turkmanovic/OpenEPT/GUI/OpenEPT/images/timerOn.png

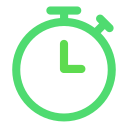
GUI/OpenEPT/images/timerOn.png
