turkmanovic/OpenEPT/Hardware/Source Files KiCad/ALTIUM_EMBEDDED_MODELS/DPAK254P1524X483-3L.step

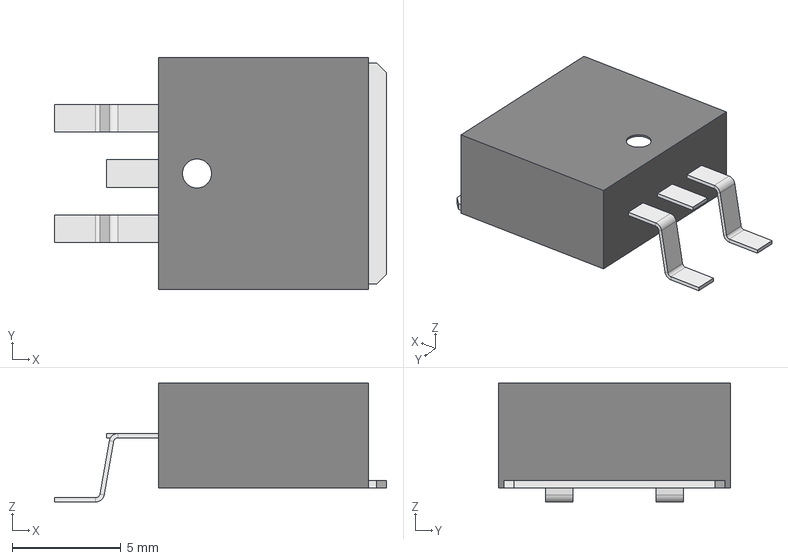
[picture p17: CAD file, 2024-06-27]
Hardware/Source Files KiCad/ALTIUM_EMBEDDED_MODELS/DPAK254P1524X483-3L.step
15.2 x 10.7 x 5.46 mm
Lead x 2
Trimmed Lead
