turkmanovic/OpenEPT/Hardware/Source Files KiCad/ALTIUM_EMBEDDED_MODELS/c-282834-2-c-3d.stp

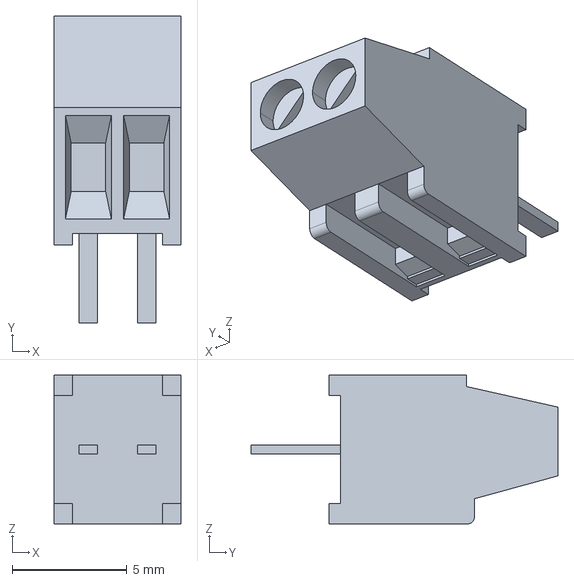
[picture p18: CAD file, 2024-06-27]
Hardware/Source Files KiCad/ALTIUM_EMBEDDED_MODELS/c-282834-2-c-3d.stp
5.54 x 13.4 x 6.50 mm
