turkmanovic/OpenEPT/Hardware/Source Files KiCad/ALTIUM_EMBEDDED_MODELS/User Library-CR3216-1206.step

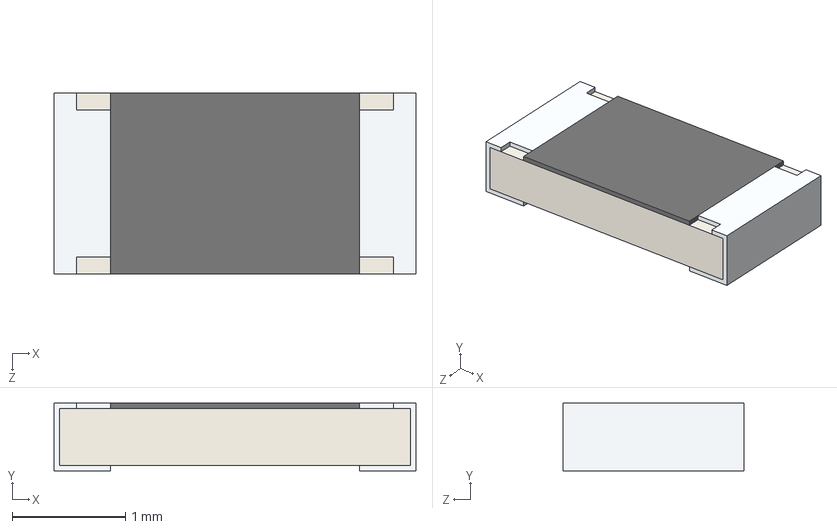
[picture p19: CAD file, 2024-06-27]
Hardware/Source Files KiCad/ALTIUM_EMBEDDED_MODELS/User Library-CR3216-1206.step
3.20 x 0.6 x 1.60 mm
