turkmanovic/OpenEPT/Hardware/Source Files KiCad/ALTIUM_EMBEDDED_MODELS/User Library-User Library-CAP_Al_SMD_6_3x7_7mm.step

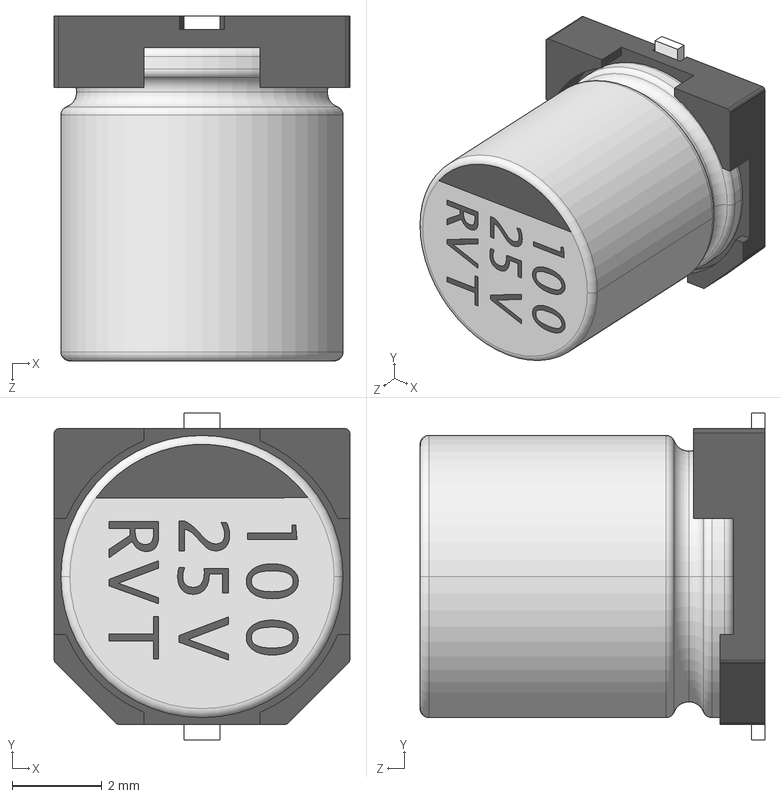
[picture p20: CAD file, 2024-06-27]
Hardware/Source Files KiCad/ALTIUM_EMBEDDED_MODELS/User Library-User Library-CAP_Al_SMD_6_3x7_7mm.step
6.60 x 7.30 x 7.70 mm
