turkmanovic/OpenEPT/Hardware/Source Files KiCad/ALTIUM_EMBEDDED_MODELS/DIOM5026X23N.step

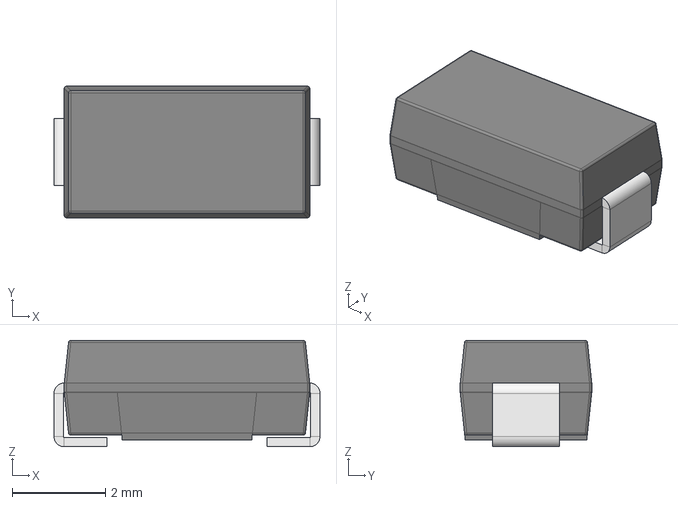
[picture p21: CAD file, 2024-06-27]
Hardware/Source Files KiCad/ALTIUM_EMBEDDED_MODELS/DIOM5026X23N.step
5.72 x 2.83 x 2.29 mm
Lead x 2
