turkmanovic/OpenEPT/Hardware/Source Files KiCad/ALTIUM_EMBEDDED_MODELS/SOIC127P600X175-8N.step

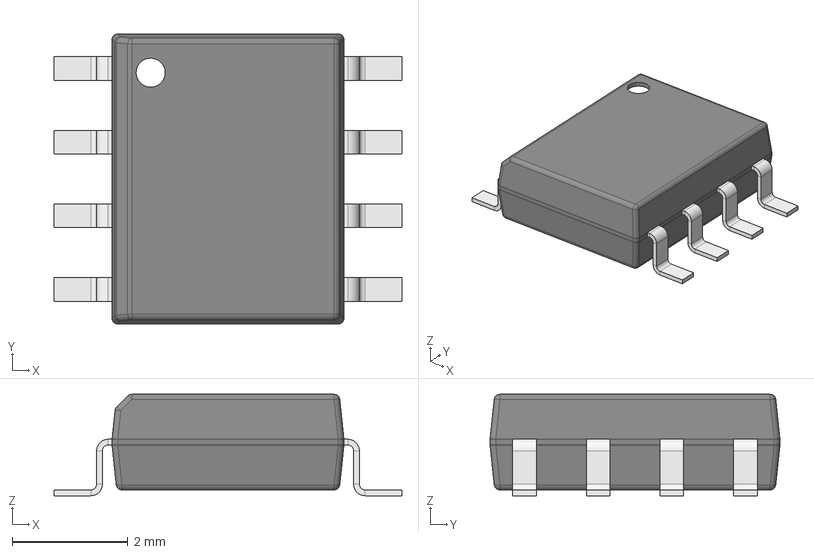
[picture p22: CAD file, 2024-06-27]
Hardware/Source Files KiCad/ALTIUM_EMBEDDED_MODELS/SOIC127P600X175-8N.step
6.00 x 5.00 x 1.75 mm
Leader x 8
