turkmanovic/OpenEPT/Hardware/Source Files KiCad/ALTIUM_EMBEDDED_MODELS/User Library-SMD Polymer Aluminum Electrolytic Capacitors B6 22uF 16V.step

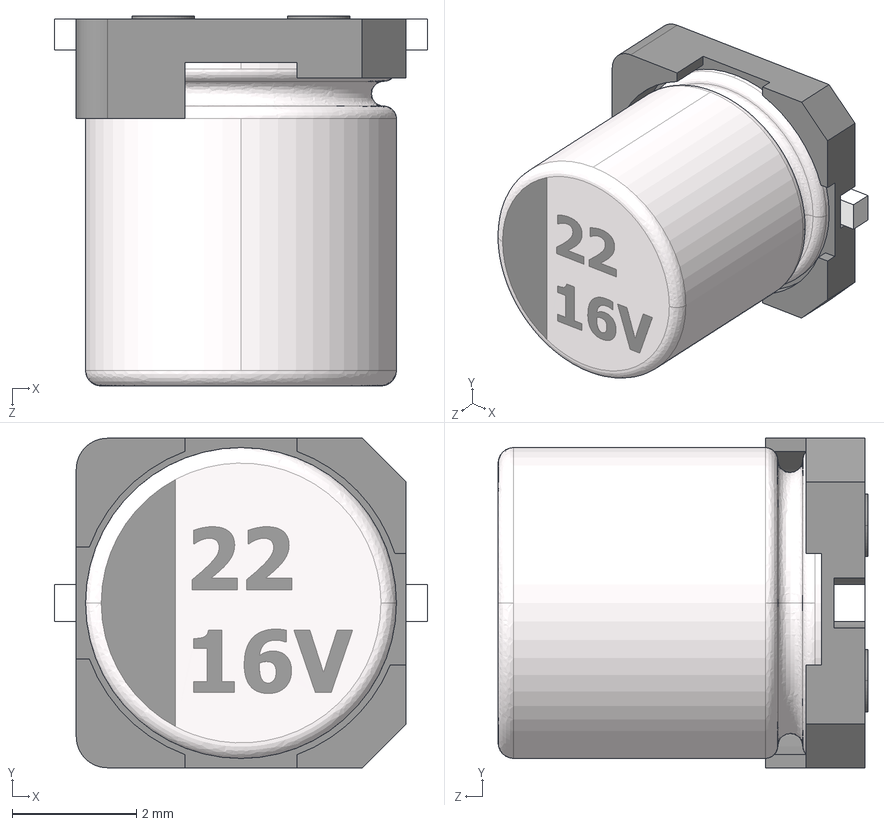
[picture p23: CAD file, 2024-06-27]
Hardware/Source Files KiCad/ALTIUM_EMBEDDED_MODELS/User Library-SMD Polymer Aluminum Electrolytic Capacitors B6 22uF 16V.step
6.00 x 5.30 x 5.95 mm
