turkmanovic/OpenEPT/Hardware/Source Files KiCad/ALTIUM_EMBEDDED_MODELS/User Library-sw_diptronics_dtsm-61r-b.step

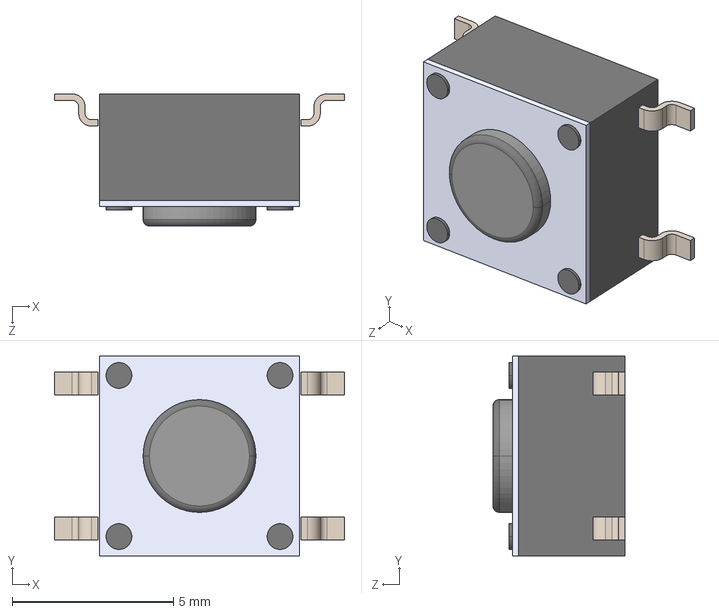
[picture p24: CAD file, 2024-06-27]
Hardware/Source Files KiCad/ALTIUM_EMBEDDED_MODELS/User Library-sw_diptronics_dtsm-61r-b.step
9.00 x 6.20 x 4.10 mm
