turkmanovic/OpenEPT/Hardware/Source Files KiCad/ALTIUM_EMBEDDED_MODELS/User Library-UWT1C100MCL1GB.step

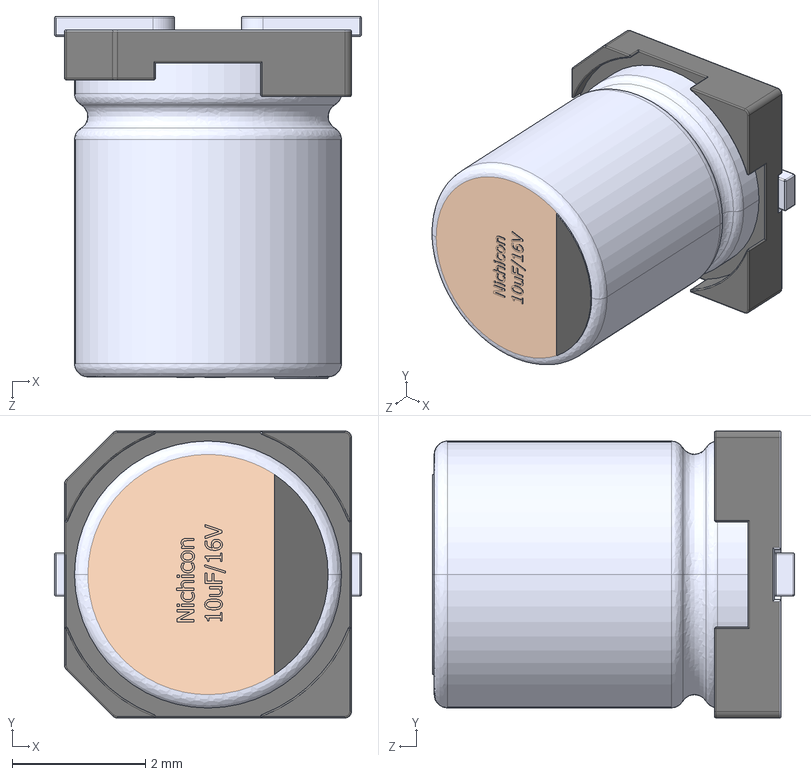
[picture p25: CAD file, 2024-06-27]
Hardware/Source Files KiCad/ALTIUM_EMBEDDED_MODELS/User Library-UWT1C100MCL1GB.step
4.60 x 4.30 x 5.43 mm
