turkmanovic/OpenEPT/Hardware/Source Files KiCad/ALTIUM_EMBEDDED_MODELS/SSQ-110-02-T-D-RA.stp

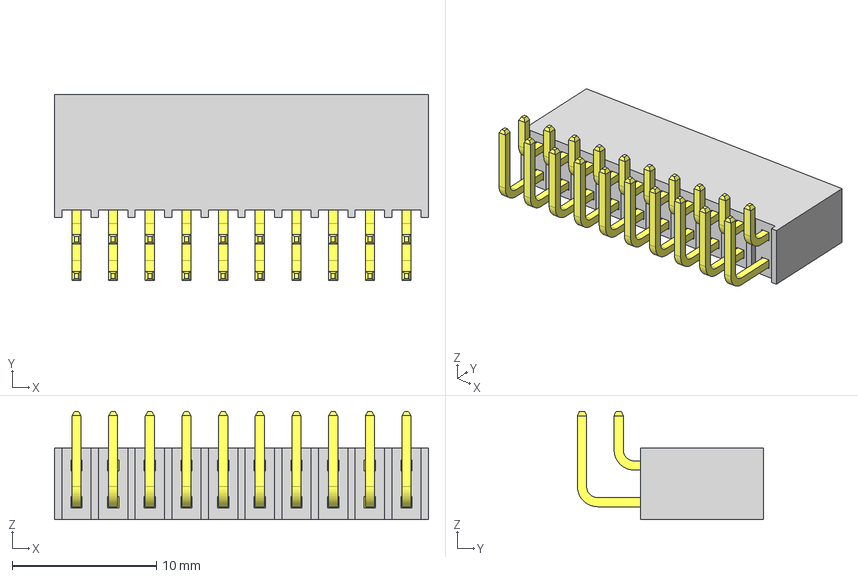
[picture p26: CAD file, 2024-06-27]
Hardware/Source Files KiCad/ALTIUM_EMBEDDED_MODELS/SSQ-110-02-T-D-RA.stp
25.9 x 12.9 x 7.49 mm
P2SSQ-110-02-T-D-RA
T1SSQ-110-02-T-D-RA
