turkmanovic/OpenEPT/GUI/OpenEPT/Chart/qcustomplot.h

/***************************************************************************
**                                                                        **
**  QCustomPlot, an easy to use, modern plotting widget for Qt            **
**  Copyright (C) 2011-2021 Emanuel Eichhammer                            **
**                                                                        **
**  This program is free software: you can redistribute it and/or modify  **
**  it under the terms of the GNU General Public License as published by  **
**  the Free Software Foundation, either version 3 of the License, or     **
**  (at your option) any later version.                                   **
**                                                                        **
**  This program is distributed in the hope that it will be useful,       **
**  but WITHOUT ANY WARRANTY; without even the implied warranty of        **
**  MERCHANTABILITY or FITNESS FOR A PARTICULAR PURPOSE.  See the         **
**  GNU General Public License for more details.                          **
**                                                                        **
**  You should have received a copy of the GNU General Public License     **
**  along with this program.  If not, see http://www.gnu.org/licenses/.   **
**                                                                        **
****************************************************************************
**           Author: Emanuel Eichhammer                                   **
**  Website/Contact: http://www.qcustomplot.com/                          **
**             Date: 29.03.21                                             **
**          Version: 2.1.0                                                **
****************************************************************************/

#ifndef QCUSTOMPLOT_H
#define QCUSTOMPLOT_H

#include <QtCore/qglobal.h>

// some Qt version/configuration dependent macros to include or exclude certain code paths:
#ifdef QCUSTOMPLOT_USE_OPENGL
#  if QT_VERSION < QT_VERSION_CHECK(5, 0, 0)
#    define QCP_OPENGL_PBUFFER
#  else
#    define QCP_OPENGL_FBO
#  endif
#  if QT_VERSION >= QT_VERSION_CHECK(5, 3, 0)
#    define QCP_OPENGL_OFFSCREENSURFACE
#  endif
#endif

#if QT_VERSION >= QT_VERSION_CHECK(5, 4, 0)
#  define QCP_DEVICEPIXELRATIO_SUPPORTED
#  if QT_VERSION >= QT_VERSION_CHECK(5, 6, 0)
#    define QCP_DEVICEPIXELRATIO_FLOAT
#  endif
#endif

#include <QtCore/QObject>
#include <QtCore/QPointer>
#include <QtCore/QSharedPointer>
#include <QtCore/QTimer>
#include <QtGui/QPainter>
#include <QtGui/QPainterPath>
#include <QtGui/QPaintEvent>
#include <QtGui/QMouseEvent>
#include <QtGui/QWheelEvent>
#include <QtGui/QPixmap>
#include <QtCore/QVector>
#include <QtCore/QString>
#include <QtCore/QDateTime>
#include <QtCore/QMultiMap>
#include <QtCore/QFlags>
#include <QtCore/QDebug>
#include <QtCore/QStack>
#include <QtCore/QCache>
#include <QtCore/QMargins>
#include <qmath.h>
#include <limits>
#include <algorithm>
#ifdef QCP_OPENGL_FBO
#  include <QtGui/QOpenGLContext>
#  if QT_VERSION < QT_VERSION_CHECK(6, 0, 0)
#    include <QtGui/QOpenGLFramebufferObject>
#  else
#    include <QOpenGLFramebufferObject>
#    include <QOpenGLPaintDevice>
#  endif
#  ifdef QCP_OPENGL_OFFSCREENSURFACE
#    include <QtGui/QOffscreenSurface>
#  else
#    include <QtGui/QWindow>
#  endif
#endif
#ifdef QCP_OPENGL_PBUFFER
#  include <QtOpenGL/QGLPixelBuffer>
#endif
#if QT_VERSION < QT_VERSION_CHECK(5, 0, 0)
#  include <qnumeric.h>
#  include <QtGui/QWidget>
#  include <QtGui/QPrinter>
#  include <QtGui/QPrintEngine>
#else
#  include <QtNumeric>
#  include <QtWidgets/QWidget>
#  include <QtPrintSupport/QtPrintSupport>
#endif
#if QT_VERSION >= QT_VERSION_CHECK(4, 8, 0)
#  include <QtCore/QElapsedTimer>
#endif
# if QT_VERSION >= QT_VERSION_CHECK(5, 2, 0)
#  include <QtCore/QTimeZone>
#endif

class QCPPainter;
class QCustomPlot;
class QCPLayerable;
class QCPLayoutElement;
class QCPLayout;
class QCPAxis;
class QCPAxisRect;
class QCPAxisPainterPrivate;
class QCPAbstractPlottable;
class QCPGraph;
class QCPAbstractItem;
class QCPPlottableInterface1D;
class QCPLegend;
class QCPItemPosition;
class QCPLayer;
class QCPAbstractLegendItem;
class QCPSelectionRect;
class QCPColorMap;
class QCPColorScale;
class QCPBars;
class QCPPolarAxisRadial;
class QCPPolarAxisAngular;
class QCPPolarGrid;
class QCPPolarGraph;

/* including file 'src/global.h'            */
/* modified 2021-03-29T02:30:44, size 16981 */

#define QCUSTOMPLOT_VERSION_STR "2.1.0"
#define QCUSTOMPLOT_VERSION 0x020100

// decl definitions for shared library compilation/usage:
#if defined(QT_STATIC_BUILD)
#  define QCP_LIB_DECL
#elif defined(QCUSTOMPLOT_COMPILE_LIBRARY)
#  define QCP_LIB_DECL Q_DECL_EXPORT
#elif defined(QCUSTOMPLOT_USE_LIBRARY)
#  define QCP_LIB_DECL Q_DECL_IMPORT
#else
#  define QCP_LIB_DECL
#endif

// define empty macro for Q_DECL_OVERRIDE if it doesn't exist (Qt < 5)
#ifndef Q_DECL_OVERRIDE
#  define Q_DECL_OVERRIDE
#endif

/*!
  The QCP Namespace contains general enums, QFlags and functions used throughout the QCustomPlot
  library.

  It provides QMetaObject-based reflection of its enums and flags via \a QCP::staticMetaObject.
*/
#ifndef Q_MOC_RUN
namespace QCP {
#else
class QCP { // when in moc-run, make it look like a class, so we get Q_GADGET, Q_ENUMS/Q_FLAGS features in namespace
    Q_GADGET
    Q_ENUMS(ExportPen)
    Q_ENUMS(ResolutionUnit)
    Q_ENUMS(SignDomain)
    Q_ENUMS(MarginSide)
    Q_FLAGS(MarginSides)
    Q_ENUMS(AntialiasedElement)
    Q_FLAGS(AntialiasedElements)
    Q_ENUMS(PlottingHint)
    Q_FLAGS(PlottingHints)
    Q_ENUMS(Interaction)
    Q_FLAGS(Interactions)
    Q_ENUMS(SelectionRectMode)
    Q_ENUMS(SelectionType)
public:
#endif

/*!
  Defines the different units in which the image resolution can be specified in the export
  functions.

  \see QCustomPlot::savePng, QCustomPlot::saveJpg, QCustomPlot::saveBmp, QCustomPlot::saveRastered
*/
enum ResolutionUnit { ruDotsPerMeter       ///< Resolution is given in dots per meter (dpm)
                      ,ruDotsPerCentimeter ///< Resolution is given in dots per centimeter (dpcm)
                      ,ruDotsPerInch       ///< Resolution is given in dots per inch (DPI/PPI)
};

/*!
  Defines how cosmetic pens (pens with numerical width 0) are handled during export.

  \see QCustomPlot::savePdf
*/
enum ExportPen { epNoCosmetic     ///< Cosmetic pens are converted to pens with pixel width 1 when exporting
                 ,epAllowCosmetic ///< Cosmetic pens are exported normally (e.g. in PDF exports, cosmetic pens always appear as 1 pixel on screen, independent of viewer zoom level)
};

/*!
  Represents negative and positive sign domain, e.g. for passing to \ref
  QCPAbstractPlottable::getKeyRange and \ref QCPAbstractPlottable::getValueRange.

  This is primarily needed when working with logarithmic axis scales, since only one of the sign
  domains can be visible at a time.
*/
enum SignDomain { sdNegative  ///< The negative sign domain, i.e. numbers smaller than zero
                  ,sdBoth     ///< Both sign domains, including zero, i.e. all numbers
                  ,sdPositive ///< The positive sign domain, i.e. numbers greater than zero
};

/*!
  Defines the sides of a rectangular entity to which margins can be applied.

  \see QCPLayoutElement::setAutoMargins, QCPAxisRect::setAutoMargins
*/
enum MarginSide { msLeft     = 0x01 ///< <tt>0x01</tt> left margin
                  ,msRight   = 0x02 ///< <tt>0x02</tt> right margin
                  ,msTop     = 0x04 ///< <tt>0x04</tt> top margin
                  ,msBottom  = 0x08 ///< <tt>0x08</tt> bottom margin
                  ,msAll     = 0xFF ///< <tt>0xFF</tt> all margins
                  ,msNone    = 0x00 ///< <tt>0x00</tt> no margin
};
Q_DECLARE_FLAGS(MarginSides, MarginSide)

/*!
  Defines what objects of a plot can be forcibly drawn antialiased/not antialiased. If an object is
  neither forcibly drawn antialiased nor forcibly drawn not antialiased, it is up to the respective
  element how it is drawn. Typically it provides a \a setAntialiased function for this.

  \c AntialiasedElements is a flag of or-combined elements of this enum type.

  \see QCustomPlot::setAntialiasedElements, QCustomPlot::setNotAntialiasedElements
*/
enum AntialiasedElement { aeAxes           = 0x0001 ///< <tt>0x0001</tt> Axis base line and tick marks
                          ,aeGrid          = 0x0002 ///< <tt>0x0002</tt> Grid lines
                          ,aeSubGrid       = 0x0004 ///< <tt>0x0004</tt> Sub grid lines
                          ,aeLegend        = 0x0008 ///< <tt>0x0008</tt> Legend box
                          ,aeLegendItems   = 0x0010 ///< <tt>0x0010</tt> Legend items
                          ,aePlottables    = 0x0020 ///< <tt>0x0020</tt> Main lines of plottables
                          ,aeItems         = 0x0040 ///< <tt>0x0040</tt> Main lines of items
                          ,aeScatters      = 0x0080 ///< <tt>0x0080</tt> Scatter symbols of plottables (excluding scatter symbols of type ssPixmap)
                          ,aeFills         = 0x0100 ///< <tt>0x0100</tt> Borders of fills (e.g. under or between graphs)
                          ,aeZeroLine      = 0x0200 ///< <tt>0x0200</tt> Zero-lines, see \ref QCPGrid::setZeroLinePen
                          ,aeOther         = 0x8000 ///< <tt>0x8000</tt> Other elements that don't fit into any of the existing categories
                          ,aeAll           = 0xFFFF ///< <tt>0xFFFF</tt> All elements
                          ,aeNone          = 0x0000 ///< <tt>0x0000</tt> No elements
};
Q_DECLARE_FLAGS(AntialiasedElements, AntialiasedElement)

/*!
  Defines plotting hints that control various aspects of the quality and speed of plotting.

  \see QCustomPlot::setPlottingHints
*/
enum PlottingHint { phNone              = 0x000 ///< <tt>0x000</tt> No hints are set
                    ,phFastPolylines    = 0x001 ///< <tt>0x001</tt> Graph/Curve lines are drawn with a faster method. This reduces the quality especially of the line segment
                    ///<                joins, thus is most effective for pen sizes larger than 1. It is only used for solid line pens.
                    ,phImmediateRefresh = 0x002 ///< <tt>0x002</tt> causes an immediate repaint() instead of a soft update() when QCustomPlot::replot() is called with parameter \ref QCustomPlot::rpRefreshHint.
                    ///<                This is set by default to prevent the plot from freezing on fast consecutive replots (e.g. user drags ranges with mouse).
                    ,phCacheLabels      = 0x004 ///< <tt>0x004</tt> axis (tick) labels will be cached as pixmaps, increasing replot performance.
};
Q_DECLARE_FLAGS(PlottingHints, PlottingHint)

/*!
  Defines the mouse interactions possible with QCustomPlot.

  \c Interactions is a flag of or-combined elements of this enum type.

  \see QCustomPlot::setInteractions
*/
enum Interaction { iNone              = 0x000 ///< <tt>0x000</tt> None of the interactions are possible
                   ,iRangeDrag        = 0x001 ///< <tt>0x001</tt> Axis ranges are draggable (see \ref QCPAxisRect::setRangeDrag, \ref QCPAxisRect::setRangeDragAxes)
                   ,iRangeZoom        = 0x002 ///< <tt>0x002</tt> Axis ranges are zoomable with the mouse wheel (see \ref QCPAxisRect::setRangeZoom, \ref QCPAxisRect::setRangeZoomAxes)
                   ,iMultiSelect      = 0x004 ///< <tt>0x004</tt> The user can select multiple objects by holding the modifier set by \ref QCustomPlot::setMultiSelectModifier while clicking
                   ,iSelectPlottables = 0x008 ///< <tt>0x008</tt> Plottables are selectable (e.g. graphs, curves, bars,... see QCPAbstractPlottable)
                   ,iSelectAxes       = 0x010 ///< <tt>0x010</tt> Axes are selectable (or parts of them, see QCPAxis::setSelectableParts)
                   ,iSelectLegend     = 0x020 ///< <tt>0x020</tt> Legends are selectable (or their child items, see QCPLegend::setSelectableParts)
                   ,iSelectItems      = 0x040 ///< <tt>0x040</tt> Items are selectable (Rectangles, Arrows, Textitems, etc. see \ref QCPAbstractItem)
                   ,iSelectOther      = 0x080 ///< <tt>0x080</tt> All other objects are selectable (e.g. your own derived layerables, other layout elements,...)
                   ,iSelectPlottablesBeyondAxisRect = 0x100 ///< <tt>0x100</tt> When performing plottable selection/hit tests, this flag extends the sensitive area beyond the axis rect
};
Q_DECLARE_FLAGS(Interactions, Interaction)

/*!
  Defines the behaviour of the selection rect.

  \see QCustomPlot::setSelectionRectMode, QCustomPlot::selectionRect, QCPSelectionRect
*/
enum SelectionRectMode { srmNone    ///< The selection rect is disabled, and all mouse events are forwarded to the underlying objects, e.g. for axis range dragging
                         ,srmZoom   ///< When dragging the mouse, a selection rect becomes active. Upon releasing, the axes that are currently set as range zoom axes (\ref QCPAxisRect::setRangeZoomAxes) will have their ranges zoomed accordingly.
                         ,srmSelect ///< When dragging the mouse, a selection rect becomes active. Upon releasing, plottable data points that were within the selection rect are selected, if the plottable's selectability setting permits. (See  \ref dataselection "data selection mechanism" for details.)
                         ,srmCustom ///< When dragging the mouse, a selection rect becomes active. It is the programmer's responsibility to connect according slots to the selection rect's signals (e.g. \ref QCPSelectionRect::accepted) in order to process the user interaction.
};

/*!
  Defines the different ways a plottable can be selected. These images show the effect of the
  different selection types, when the indicated selection rect was dragged:

  <center>
  <table>
  <tr>
    <td>\image html selectiontype-none.png stNone</td>
    <td>\image html selectiontype-whole.png stWhole</td>
    <td>\image html selectiontype-singledata.png stSingleData</td>
    <td>\image html selectiontype-datarange.png stDataRange</td>
    <td>\image html selectiontype-multipledataranges.png stMultipleDataRanges</td>
  </tr>
  </table>
  </center>

  \see QCPAbstractPlottable::setSelectable, QCPDataSelection::enforceType
*/
enum SelectionType { stNone                ///< The plottable is not selectable
                     ,stWhole              ///< Selection behaves like \ref stMultipleDataRanges, but if there are any data points selected, the entire plottable is drawn as selected.
                     ,stSingleData         ///< One individual data point can be selected at a time
                     ,stDataRange          ///< Multiple contiguous data points (a data range) can be selected
                     ,stMultipleDataRanges ///< Any combination of data points/ranges can be selected
};

/*! \internal

  Returns whether the specified \a value is considered an invalid data value for plottables (i.e.
  is \e nan or \e +/-inf). This function is used to check data validity upon replots, when the
  compiler flag \c QCUSTOMPLOT_CHECK_DATA is set.
*/
inline bool isInvalidData(double value)
{
    return qIsNaN(value) || qIsInf(value);
}

/*! \internal
  \overload

  Checks two arguments instead of one.
*/
inline bool isInvalidData(double value1, double value2)
{
    return isInvalidData(value1) || isInvalidData(value2);
}

/*! \internal

  Sets the specified \a side of \a margins to \a value

  \see getMarginValue
*/
inline void setMarginValue(QMargins &margins, QCP::MarginSide side, int value)
{
    switch (side)
    {
    case QCP::msLeft: margins.setLeft(value); break;
    case QCP::msRight: margins.setRight(value); break;
    case QCP::msTop: margins.setTop(value); break;
    case QCP::msBottom: margins.setBottom(value); break;
    case QCP::msAll: margins = QMargins(value, value, value, value); break;
    default: break;
    }
}

/*! \internal

  Returns the value of the specified \a side of \a margins. If \a side is \ref QCP::msNone or
  \ref QCP::msAll, returns 0.

  \see setMarginValue
*/
inline int getMarginValue(const QMargins &margins, QCP::MarginSide side)
{
    switch (side)
    {
    case QCP::msLeft: return margins.left();
    case QCP::msRight: return margins.right();
    case QCP::msTop: return margins.top();
    case QCP::msBottom: return margins.bottom();
    default: break;
    }
    return 0;
}


extern const QMetaObject staticMetaObject; // in moc-run we create a static meta object for QCP "fake" object. This line is the link to it via QCP::staticMetaObject in normal operation as namespace

} // end of namespace QCP
Q_DECLARE_OPERATORS_FOR_FLAGS(QCP::AntialiasedElements)
Q_DECLARE_OPERATORS_FOR_FLAGS(QCP::PlottingHints)
Q_DECLARE_OPERATORS_FOR_FLAGS(QCP::MarginSides)
Q_DECLARE_OPERATORS_FOR_FLAGS(QCP::Interactions)
Q_DECLARE_METATYPE(QCP::ExportPen)
Q_DECLARE_METATYPE(QCP::ResolutionUnit)
Q_DECLARE_METATYPE(QCP::SignDomain)
Q_DECLARE_METATYPE(QCP::MarginSide)
Q_DECLARE_METATYPE(QCP::AntialiasedElement)
Q_DECLARE_METATYPE(QCP::PlottingHint)
Q_DECLARE_METATYPE(QCP::Interaction)
Q_DECLARE_METATYPE(QCP::SelectionRectMode)
Q_DECLARE_METATYPE(QCP::SelectionType)

/* end of 'src/global.h' */


/* including file 'src/vector2d.h'         */
/* modified 2021-03-29T02:30:44, size 4988 */

class QCP_LIB_DECL QCPVector2D
{
public:
    QCPVector2D();
    QCPVector2D(double x, double y);
    QCPVector2D(const QPoint &point);
    QCPVector2D(const QPointF &point);

    // getters:
    double x() const { return mX; }
    double y() const { return mY; }
    double &rx() { return mX; }
    double &ry() { return mY; }

    // setters:
    void setX(double x) { mX = x; }
    void setY(double y) { mY = y; }

    // non-virtual methods:
    double length() const { return qSqrt(mX*mX+mY*mY); }
    double lengthSquared() const { return mX*mX+mY*mY; }
    double angle() const { return qAtan2(mY, mX); }
    QPoint toPoint() const { return QPoint(int(mX), int(mY)); }
    QPointF toPointF() const { return QPointF(mX, mY); }

    bool isNull() const { return qIsNull(mX) && qIsNull(mY); }
    void normalize();
    QCPVector2D normalized() const;
    QCPVector2D perpendicular() const { return QCPVector2D(-mY, mX); }
    double dot(const QCPVector2D &vec) const { return mX*vec.mX+mY*vec.mY; }
    double distanceSquaredToLine(const QCPVector2D &start, const QCPVector2D &end) const;
    double distanceSquaredToLine(const QLineF &line) const;
    double distanceToStraightLine(const QCPVector2D &base, const QCPVector2D &direction) const;

    QCPVector2D &operator*=(double factor);
    QCPVector2D &operator/=(double divisor);
    QCPVector2D &operator+=(const QCPVector2D &vector);
    QCPVector2D &operator-=(const QCPVector2D &vector);

private:
    // property members:
    double mX, mY;

    friend inline const QCPVector2D operator*(double factor, const QCPVector2D &vec);
    friend inline const QCPVector2D operator*(const QCPVector2D &vec, double factor);
    friend inline const QCPVector2D operator/(const QCPVector2D &vec, double divisor);
    friend inline const QCPVector2D operator+(const QCPVector2D &vec1, const QCPVector2D &vec2);
    friend inline const QCPVector2D operator-(const QCPVector2D &vec1, const QCPVector2D &vec2);
    friend inline const QCPVector2D operator-(const QCPVector2D &vec);
};
Q_DECLARE_TYPEINFO(QCPVector2D, Q_MOVABLE_TYPE);

inline const QCPVector2D operator*(double factor, const QCPVector2D &vec) { return QCPVector2D(vec.mX*factor, vec.mY*factor); }
inline const QCPVector2D operator*(const QCPVector2D &vec, double factor) { return QCPVector2D(vec.mX*factor, vec.mY*factor); }
inline const QCPVector2D operator/(const QCPVector2D &vec, double divisor) { return QCPVector2D(vec.mX/divisor, vec.mY/divisor); }
inline const QCPVector2D operator+(const QCPVector2D &vec1, const QCPVector2D &vec2) { return QCPVector2D(vec1.mX+vec2.mX, vec1.mY+vec2.mY); }
inline const QCPVector2D operator-(const QCPVector2D &vec1, const QCPVector2D &vec2) { return QCPVector2D(vec1.mX-vec2.mX, vec1.mY-vec2.mY); }
inline const QCPVector2D operator-(const QCPVector2D &vec) { return QCPVector2D(-vec.mX, -vec.mY); }

/*! \relates QCPVector2D

  Prints \a vec in a human readable format to the qDebug output.
*/
inline QDebug operator<< (QDebug d, const QCPVector2D &vec)
{
    d.nospace() << "QCPVector2D(" << vec.x() << ", " << vec.y() << ")";
    return d.space();
}

/* end of 'src/vector2d.h' */


/* including file 'src/painter.h'          */
/* modified 2021-03-29T02:30:44, size 4035 */

class QCP_LIB_DECL QCPPainter : public QPainter
{
    Q_GADGET
public:
    /*!
    Defines special modes the painter can operate in. They disable or enable certain subsets of features/fixes/workarounds,
    depending on whether they are wanted on the respective output device.
  */
    enum PainterMode { pmDefault       = 0x00   ///< <tt>0x00</tt> Default mode for painting on screen devices
                       ,pmVectorized   = 0x01   ///< <tt>0x01</tt> Mode for vectorized painting (e.g. PDF export). For example, this prevents some antialiasing fixes.
                       ,pmNoCaching    = 0x02   ///< <tt>0x02</tt> Mode for all sorts of exports (e.g. PNG, PDF,...). For example, this prevents using cached pixmap labels
                       ,pmNonCosmetic  = 0x04   ///< <tt>0x04</tt> Turns pen widths 0 to 1, i.e. disables cosmetic pens. (A cosmetic pen is always drawn with width 1 pixel in the vector image/pdf viewer, independent of zoom.)
    };
    Q_ENUMS(PainterMode)
    Q_FLAGS(PainterModes)
    Q_DECLARE_FLAGS(PainterModes, PainterMode)

    QCPPainter();
    explicit QCPPainter(QPaintDevice *device);

    // getters:
    bool antialiasing() const { return testRenderHint(QPainter::Antialiasing); }
    PainterModes modes() const { return mModes; }

    // setters:
    void setAntialiasing(bool enabled);
    void setMode(PainterMode mode, bool enabled=true);
    void setModes(PainterModes modes);

    // methods hiding non-virtual base class functions (QPainter bug workarounds):
    bool begin(QPaintDevice *device);
    void setPen(const QPen &pen);
    void setPen(const QColor &color);
    void setPen(Qt::PenStyle penStyle);
    void drawLine(const QLineF &line);
    void drawLine(const QPointF &p1, const QPointF &p2) {drawLine(QLineF(p1, p2));}
    void save();
    void restore();

    // non-virtual methods:
    void makeNonCosmetic();

protected:
    // property members:
    PainterModes mModes;
    bool mIsAntialiasing;

    // non-property members:
    QStack<bool> mAntialiasingStack;
};
Q_DECLARE_OPERATORS_FOR_FLAGS(QCPPainter::PainterModes)
Q_DECLARE_METATYPE(QCPPainter::PainterMode)

/* end of 'src/painter.h' */


/* including file 'src/paintbuffer.h'      */
/* modified 2021-03-29T02:30:44, size 5006 */

class QCP_LIB_DECL QCPAbstractPaintBuffer
{
public:
    explicit QCPAbstractPaintBuffer(const QSize &size, double devicePixelRatio);
    virtual ~QCPAbstractPaintBuffer();

    // getters:
    QSize size() const { return mSize; }
    bool invalidated() const { return mInvalidated; }
    double devicePixelRatio() const { return mDevicePixelRatio; }

    // setters:
    void setSize(const QSize &size);
    void setInvalidated(bool invalidated=true);
    void setDevicePixelRatio(double ratio);

    // introduced virtual methods:
    virtual QCPPainter *startPainting() = 0;
    virtual void donePainting() {}
    virtual void draw(QCPPainter *painter) const = 0;
    virtual void clear(const QColor &color) = 0;

protected:
    // property members:
    QSize mSize;
    double mDevicePixelRatio;

    // non-property members:
    bool mInvalidated;

    // introduced virtual methods:
    virtual void reallocateBuffer() = 0;
};


class QCP_LIB_DECL QCPPaintBufferPixmap : public QCPAbstractPaintBuffer
{
public:
    explicit QCPPaintBufferPixmap(const QSize &size, double devicePixelRatio);
    virtual ~QCPPaintBufferPixmap() Q_DECL_OVERRIDE;

    // reimplemented virtual methods:
    virtual QCPPainter *startPainting() Q_DECL_OVERRIDE;
    virtual void draw(QCPPainter *painter) const Q_DECL_OVERRIDE;
    void clear(const QColor &color) Q_DECL_OVERRIDE;

protected:
    // non-property members:
    QPixmap mBuffer;

    // reimplemented virtual methods:
    virtual void reallocateBuffer() Q_DECL_OVERRIDE;
};


#ifdef QCP_OPENGL_PBUFFER
class QCP_LIB_DECL QCPPaintBufferGlPbuffer : public QCPAbstractPaintBuffer
{
public:
    explicit QCPPaintBufferGlPbuffer(const QSize &size, double devicePixelRatio, int multisamples);
    virtual ~QCPPaintBufferGlPbuffer() Q_DECL_OVERRIDE;

    // reimplemented virtual methods:
    virtual QCPPainter *startPainting() Q_DECL_OVERRIDE;
    virtual void draw(QCPPainter *painter) const Q_DECL_OVERRIDE;
    void clear(const QColor &color) Q_DECL_OVERRIDE;

protected:
    // non-property members:
    QGLPixelBuffer *mGlPBuffer;
    int mMultisamples;

    // reimplemented virtual methods:
    virtual void reallocateBuffer() Q_DECL_OVERRIDE;
};
#endif // QCP_OPENGL_PBUFFER


#ifdef QCP_OPENGL_FBO
class QCP_LIB_DECL QCPPaintBufferGlFbo : public QCPAbstractPaintBuffer
{
public:
    explicit QCPPaintBufferGlFbo(const QSize &size, double devicePixelRatio, QWeakPointer<QOpenGLContext> glContext, QWeakPointer<QOpenGLPaintDevice> glPaintDevice);
    virtual ~QCPPaintBufferGlFbo() Q_DECL_OVERRIDE;

    // reimplemented virtual methods:
    virtual QCPPainter *startPainting() Q_DECL_OVERRIDE;
    virtual void donePainting() Q_DECL_OVERRIDE;
    virtual void draw(QCPPainter *painter) const Q_DECL_OVERRIDE;
    void clear(const QColor &color) Q_DECL_OVERRIDE;

protected:
    // non-property members:
    QWeakPointer<QOpenGLContext> mGlContext;
    QWeakPointer<QOpenGLPaintDevice> mGlPaintDevice;
    QOpenGLFramebufferObject *mGlFrameBuffer;

    // reimplemented virtual methods:
    virtual void reallocateBuffer() Q_DECL_OVERRIDE;
};
#endif // QCP_OPENGL_FBO

/* end of 'src/paintbuffer.h' */


/* including file 'src/layer.h'            */
/* modified 2021-03-29T02:30:44, size 7038 */

class QCP_LIB_DECL QCPLayer : public QObject
{
    Q_OBJECT
    /// \cond INCLUDE_QPROPERTIES
    Q_PROPERTY(QCustomPlot* parentPlot READ parentPlot)
    Q_PROPERTY(QString name READ name)
    Q_PROPERTY(int index READ index)
    Q_PROPERTY(QList<QCPLayerable*> children READ children)
    Q_PROPERTY(bool visible READ visible WRITE setVisible)
    Q_PROPERTY(LayerMode mode READ mode WRITE setMode)
    /// \endcond
public:

    /*!
    Defines the different rendering modes of a layer. Depending on the mode, certain layers can be
    replotted individually, without the need to replot (possibly complex) layerables on other
    layers.

    \see setMode
  */
    enum LayerMode { lmLogical   ///< Layer is used only for rendering order, and shares paint buffer with all other adjacent logical layers.
                     ,lmBuffered ///< Layer has its own paint buffer and may be replotted individually (see \ref replot).
    };
    Q_ENUMS(LayerMode)

    QCPLayer(QCustomPlot* parentPlot, const QString &layerName);
    virtual ~QCPLayer();

    // getters:
    QCustomPlot *parentPlot() const { return mParentPlot; }
    QString name() const { return mName; }
    int index() const { return mIndex; }
    QList<QCPLayerable*> children() const { return mChildren; }
    bool visible() const { return mVisible; }
    LayerMode mode() const { return mMode; }

    // setters:
    void setVisible(bool visible);
    void setMode(LayerMode mode);

    // non-virtual methods:
    void replot();

protected:
    // property members:
    QCustomPlot *mParentPlot;
    QString mName;
    int mIndex;
    QList<QCPLayerable*> mChildren;
    bool mVisible;
    LayerMode mMode;

    // non-property members:
    QWeakPointer<QCPAbstractPaintBuffer> mPaintBuffer;

    // non-virtual methods:
    void draw(QCPPainter *painter);
    void drawToPaintBuffer();
    void addChild(QCPLayerable *layerable, bool prepend);
    void removeChild(QCPLayerable *layerable);

private:
    Q_DISABLE_COPY(QCPLayer)

    friend class QCustomPlot;
    friend class QCPLayerable;
};
Q_DECLARE_METATYPE(QCPLayer::LayerMode)

class QCP_LIB_DECL QCPLayerable : public QObject
{
    Q_OBJECT
    /// \cond INCLUDE_QPROPERTIES
    Q_PROPERTY(bool visible READ visible WRITE setVisible)
    Q_PROPERTY(QCustomPlot* parentPlot READ parentPlot)
    Q_PROPERTY(QCPLayerable* parentLayerable READ parentLayerable)
    Q_PROPERTY(QCPLayer* layer READ layer WRITE setLayer NOTIFY layerChanged)
    Q_PROPERTY(bool antialiased READ antialiased WRITE setAntialiased)
    /// \endcond
public:
    QCPLayerable(QCustomPlot *plot, QString targetLayer=QString(), QCPLayerable *parentLayerable=nullptr);
    virtual ~QCPLayerable();

    // getters:
    bool visible() const { return mVisible; }
    QCustomPlot *parentPlot() const { return mParentPlot; }
    QCPLayerable *parentLayerable() const { return mParentLayerable.data(); }
    QCPLayer *layer() const { return mLayer; }
    bool antialiased() const { return mAntialiased; }

    // setters:
    void setVisible(bool on);
    Q_SLOT bool setLayer(QCPLayer *layer);
    bool setLayer(const QString &layerName);
    void setAntialiased(bool enabled);

    // introduced virtual methods:
    virtual double selectTest(const QPointF &pos, bool onlySelectable, QVariant *details=nullptr) const;

    // non-property methods:
    bool realVisibility() const;

signals:
    void layerChanged(QCPLayer *newLayer);

protected:
    // property members:
    bool mVisible;
    QCustomPlot *mParentPlot;
    QPointer<QCPLayerable> mParentLayerable;
    QCPLayer *mLayer;
    bool mAntialiased;

    // introduced virtual methods:
    virtual void parentPlotInitialized(QCustomPlot *parentPlot);
    virtual QCP::Interaction selectionCategory() const;
    virtual QRect clipRect() const;
    virtual void applyDefaultAntialiasingHint(QCPPainter *painter) const = 0;
    virtual void draw(QCPPainter *painter) = 0;
    // selection events:
    virtual void selectEvent(QMouseEvent *event, bool additive, const QVariant &details, bool *selectionStateChanged);
    virtual void deselectEvent(bool *selectionStateChanged);
    // low-level mouse events:
    virtual void mousePressEvent(QMouseEvent *event, const QVariant &details);
    virtual void mouseMoveEvent(QMouseEvent *event, const QPointF &startPos);
    virtual void mouseReleaseEvent(QMouseEvent *event, const QPointF &startPos);
    virtual void mouseDoubleClickEvent(QMouseEvent *event, const QVariant &details);
    virtual void wheelEvent(QWheelEvent *event);

    // non-property methods:
    void initializeParentPlot(QCustomPlot *parentPlot);
    void setParentLayerable(QCPLayerable* parentLayerable);
    bool moveToLayer(QCPLayer *layer, bool prepend);
    void applyAntialiasingHint(QCPPainter *painter, bool localAntialiased, QCP::AntialiasedElement overrideElement) const;

private:
    Q_DISABLE_COPY(QCPLayerable)

    friend class QCustomPlot;
    friend class QCPLayer;
    friend class QCPAxisRect;
};

/* end of 'src/layer.h' */


/* including file 'src/axis/range.h'       */
/* modified 2021-03-29T02:30:44, size 5280 */

class QCP_LIB_DECL QCPRange
{
public:
    double lower, upper;

    QCPRange();
    QCPRange(double lower, double upper);

    bool operator==(const QCPRange& other) const { return lower == other.lower && upper == other.upper; }
    bool operator!=(const QCPRange& other) const { return !(*this == other); }

    QCPRange &operator+=(const double& value) { lower+=value; upper+=value; return *this; }
    QCPRange &operator-=(const double& value) { lower-=value; upper-=value; return *this; }
    QCPRange &operator*=(const double& value) { lower*=value; upper*=value; return *this; }
    QCPRange &operator/=(const double& value) { lower/=value; upper/=value; return *this; }
    friend inline const QCPRange operator+(const QCPRange&, double);
    friend inline const QCPRange operator+(double, const QCPRange&);
    friend inline const QCPRange operator-(const QCPRange& range, double value);
    friend inline const QCPRange operator*(const QCPRange& range, double value);
    friend inline const QCPRange operator*(double value, const QCPRange& range);
    friend inline const QCPRange operator/(const QCPRange& range, double value);

    double size() const { return upper-lower; }
    double center() const { return (upper+lower)*0.5; }
    void normalize() { if (lower > upper) qSwap(lower, upper); }
    void expand(const QCPRange &otherRange);
    void expand(double includeCoord);
    QCPRange expanded(const QCPRange &otherRange) const;
    QCPRange expanded(double includeCoord) const;
    QCPRange bounded(double lowerBound, double upperBound) const;
    QCPRange sanitizedForLogScale() const;
    QCPRange sanitizedForLinScale() const;
    bool contains(double value) const { return value >= lower && value <= upper; }

    static bool validRange(double lower, double upper);
    static bool validRange(const QCPRange &range);
    static const double minRange;
    static const double maxRange;

};
Q_DECLARE_TYPEINFO(QCPRange, Q_MOVABLE_TYPE);

/*! \relates QCPRange

  Prints \a range in a human readable format to the qDebug output.
*/
inline QDebug operator<< (QDebug d, const QCPRange &range)
{
    d.nospace() << "QCPRange(" << range.lower << ", " << range.upper << ")";
    return d.space();
}

/*!
  Adds \a value to both boundaries of the range.
*/
inline const QCPRange operator+(const QCPRange& range, double value)
{
    QCPRange result(range);
    result += value;
    return result;
}

/*!
  Adds \a value to both boundaries of the range.
*/
inline const QCPRange operator+(double value, const QCPRange& range)
{
    QCPRange result(range);
    result += value;
    return result;
}

/*!
  Subtracts \a value from both boundaries of the range.
*/
inline const QCPRange operator-(const QCPRange& range, double value)
{
    QCPRange result(range);
    result -= value;
    return result;
}

/*!
  Multiplies both boundaries of the range by \a value.
*/
inline const QCPRange operator*(const QCPRange& range, double value)
{
    QCPRange result(range);
    result *= value;
    return result;
}

/*!
  Multiplies both boundaries of the range by \a value.
*/
inline const QCPRange operator*(double value, const QCPRange& range)
{
    QCPRange result(range);
    result *= value;
    return result;
}

/*!
  Divides both boundaries of the range by \a value.
*/
inline const QCPRange operator/(const QCPRange& range, double value)
{
    QCPRange result(range);
    result /= value;
    return result;
}

/* end of 'src/axis/range.h' */


/* including file 'src/selection.h'        */
/* modified 2021-03-29T02:30:44, size 8569 */

class QCP_LIB_DECL QCPDataRange
{
public:
    QCPDataRange();
    QCPDataRange(int begin, int end);

    bool operator==(const QCPDataRange& other) const { return mBegin == other.mBegin && mEnd == other.mEnd; }
    bool operator!=(const QCPDataRange& other) const { return !(*this == other); }

    // getters:
    int begin() const { return mBegin; }
    int end() const { return mEnd; }
    int size() const { return mEnd-mBegin; }
    int length() const { return size(); }

    // setters:
    void setBegin(int begin) { mBegin = begin; }
    void setEnd(int end)  { mEnd = end; }

    // non-property methods:
    bool isValid() const { return (mEnd >= mBegin) && (mBegin >= 0); }
    bool isEmpty() const { return length() == 0; }
    QCPDataRange bounded(const QCPDataRange &other) const;
    QCPDataRange expanded(const QCPDataRange &other) const;
    QCPDataRange intersection(const QCPDataRange &other) const;
    QCPDataRange adjusted(int changeBegin, int changeEnd) const { return QCPDataRange(mBegin+changeBegin, mEnd+changeEnd); }
    bool intersects(const QCPDataRange &other) const;
    bool contains(const QCPDataRange &other) const;

private:
    // property members:
    int mBegin, mEnd;

};
Q_DECLARE_TYPEINFO(QCPDataRange, Q_MOVABLE_TYPE);


class QCP_LIB_DECL QCPDataSelection
{
public:
    explicit QCPDataSelection();
    explicit QCPDataSelection(const QCPDataRange &range);

    bool operator==(const QCPDataSelection& other) const;
    bool operator!=(const QCPDataSelection& other) const { return !(*this == other); }
    QCPDataSelection &operator+=(const QCPDataSelection& other);
    QCPDataSelection &operator+=(const QCPDataRange& other);
    QCPDataSelection &operator-=(const QCPDataSelection& other);
    QCPDataSelection &operator-=(const QCPDataRange& other);
    friend inline const QCPDataSelection operator+(const QCPDataSelection& a, const QCPDataSelection& b);
    friend inline const QCPDataSelection operator+(const QCPDataRange& a, const QCPDataSelection& b);
    friend inline const QCPDataSelection operator+(const QCPDataSelection& a, const QCPDataRange& b);
    friend inline const QCPDataSelection operator+(const QCPDataRange& a, const QCPDataRange& b);
    friend inline const QCPDataSelection operator-(const QCPDataSelection& a, const QCPDataSelection& b);
    friend inline const QCPDataSelection operator-(const QCPDataRange& a, const QCPDataSelection& b);
    friend inline const QCPDataSelection operator-(const QCPDataSelection& a, const QCPDataRange& b);
    friend inline const QCPDataSelection operator-(const QCPDataRange& a, const QCPDataRange& b);

    // getters:
    int dataRangeCount() const { return mDataRanges.size(); }
    int dataPointCount() const;
    QCPDataRange dataRange(int index=0) const;
    QList<QCPDataRange> dataRanges() const { return mDataRanges; }
    QCPDataRange span() const;

    // non-property methods:
    void addDataRange(const QCPDataRange &dataRange, bool simplify=true);
    void clear();
    bool isEmpty() const { return mDataRanges.isEmpty(); }
    void simplify();
    void enforceType(QCP::SelectionType type);
    bool contains(const QCPDataSelection &other) const;
    QCPDataSelection intersection(const QCPDataRange &other) const;
    QCPDataSelection intersection(const QCPDataSelection &other) const;
    QCPDataSelection inverse(const QCPDataRange &outerRange) const;

private:
    // property members:
    QList<QCPDataRange> mDataRanges;

    inline static bool lessThanDataRangeBegin(const QCPDataRange &a, const QCPDataRange &b) { return a.begin() < b.begin(); }
};
Q_DECLARE_METATYPE(QCPDataSelection)


/*!
  Return a \ref QCPDataSelection with the data points in \a a joined with the data points in \a b.
  The resulting data selection is already simplified (see \ref QCPDataSelection::simplify).
*/
inline const QCPDataSelection operator+(const QCPDataSelection& a, const QCPDataSelection& b)
{
    QCPDataSelection result(a);
    result += b;
    return result;
}

/*!
  Return a \ref QCPDataSelection with the data points in \a a joined with the data points in \a b.
  The resulting data selection is already simplified (see \ref QCPDataSelection::simplify).
*/
inline const QCPDataSelection operator+(const QCPDataRange& a, const QCPDataSelection& b)
{
    QCPDataSelection result(a);
    result += b;
    return result;
}

/*!
  Return a \ref QCPDataSelection with the data points in \a a joined with the data points in \a b.
  The resulting data selection is already simplified (see \ref QCPDataSelection::simplify).
*/
inline const QCPDataSelection operator+(const QCPDataSelection& a, const QCPDataRange& b)
{
    QCPDataSelection result(a);
    result += b;
    return result;
}

/*!
  Return a \ref QCPDataSelection with the data points in \a a joined with the data points in \a b.
  The resulting data selection is already simplified (see \ref QCPDataSelection::simplify).
*/
inline const QCPDataSelection operator+(const QCPDataRange& a, const QCPDataRange& b)
{
    QCPDataSelection result(a);
    result += b;
    return result;
}

/*!
  Return a \ref QCPDataSelection with the data points which are in \a a but not in \a b.
*/
inline const QCPDataSelection operator-(const QCPDataSelection& a, const QCPDataSelection& b)
{
    QCPDataSelection result(a);
    result -= b;
    return result;
}

/*!
  Return a \ref QCPDataSelection with the data points which are in \a a but not in \a b.
*/
inline const QCPDataSelection operator-(const QCPDataRange& a, const QCPDataSelection& b)
{
    QCPDataSelection result(a);
    result -= b;
    return result;
}

/*!
  Return a \ref QCPDataSelection with the data points which are in \a a but not in \a b.
*/
inline const QCPDataSelection operator-(const QCPDataSelection& a, const QCPDataRange& b)
{
    QCPDataSelection result(a);
    result -= b;
    return result;
}

/*!
  Return a \ref QCPDataSelection with the data points which are in \a a but not in \a b.
*/
inline const QCPDataSelection operator-(const QCPDataRange& a, const QCPDataRange& b)
{
    QCPDataSelection result(a);
    result -= b;
    return result;
}

/*! \relates QCPDataRange

  Prints \a dataRange in a human readable format to the qDebug output.
*/
inline QDebug operator<< (QDebug d, const QCPDataRange &dataRange)
{
    d.nospace() << "QCPDataRange(" << dataRange.begin() << ", " << dataRange.end() << ")";
    return d;
}

/*! \relates QCPDataSelection

  Prints \a selection in a human readable format to the qDebug output.
*/
inline QDebug operator<< (QDebug d, const QCPDataSelection &selection)
{
    d.nospace() << "QCPDataSelection(";
    for (int i=0; i<selection.dataRangeCount(); ++i)
    {
        if (i != 0)
            d << ", ";
        d << selection.dataRange(i);
    }
    d << ")";
    return d;
}



/* end of 'src/selection.h' */


/* including file 'src/selectionrect.h'    */
/* modified 2021-03-29T02:30:44, size 3354 */

class QCP_LIB_DECL QCPSelectionRect : public QCPLayerable
{
    Q_OBJECT
public:
    explicit QCPSelectionRect(QCustomPlot *parentPlot);
    virtual ~QCPSelectionRect() Q_DECL_OVERRIDE;

    // getters:
    QRect rect() const { return mRect; }
    QCPRange range(const QCPAxis *axis) const;
    QPen pen() const { return mPen; }
    QBrush brush() const { return mBrush; }
    bool isActive() const { return mActive; }

    // setters:
    void setPen(const QPen &pen);
    void setBrush(const QBrush &brush);

    // non-property methods:
    Q_SLOT void cancel();

signals:
    void started(QMouseEvent *event);
    void changed(const QRect &rect, QMouseEvent *event);
    void canceled(const QRect &rect, QInputEvent *event);
    void accepted(const QRect &rect, QMouseEvent *event);

protected:
    // property members:
    QRect mRect;
    QPen mPen;
    QBrush mBrush;
    // non-property members:
    bool mActive;

    // introduced virtual methods:
    virtual void startSelection(QMouseEvent *event);
    virtual void moveSelection(QMouseEvent *event);
    virtual void endSelection(QMouseEvent *event);
    virtual void keyPressEvent(QKeyEvent *event);

    // reimplemented virtual methods
    virtual void applyDefaultAntialiasingHint(QCPPainter *painter) const Q_DECL_OVERRIDE;
    virtual void draw(QCPPainter *painter) Q_DECL_OVERRIDE;

    friend class QCustomPlot;
};

/* end of 'src/selectionrect.h' */


/* including file 'src/layout.h'            */
/* modified 2021-03-29T02:30:44, size 14279 */

class QCP_LIB_DECL QCPMarginGroup : public QObject
{
    Q_OBJECT
public:
    explicit QCPMarginGroup(QCustomPlot *parentPlot);
    virtual ~QCPMarginGroup();

    // non-virtual methods:
    QList<QCPLayoutElement*> elements(QCP::MarginSide side) const { return mChildren.value(side); }
    bool isEmpty() const;
    void clear();

protected:
    // non-property members:
    QCustomPlot *mParentPlot;
    QHash<QCP::MarginSide, QList<QCPLayoutElement*> > mChildren;

    // introduced virtual methods:
    virtual int commonMargin(QCP::MarginSide side) const;

    // non-virtual methods:
    void addChild(QCP::MarginSide side, QCPLayoutElement *element);
    void removeChild(QCP::MarginSide side, QCPLayoutElement *element);

private:
    Q_DISABLE_COPY(QCPMarginGroup)

    friend class QCPLayoutElement;
};


class QCP_LIB_DECL QCPLayoutElement : public QCPLayerable
{
    Q_OBJECT
    /// \cond INCLUDE_QPROPERTIES
    Q_PROPERTY(QCPLayout* layout READ layout)
    Q_PROPERTY(QRect rect READ rect)
    Q_PROPERTY(QRect outerRect READ outerRect WRITE setOuterRect)
    Q_PROPERTY(QMargins margins READ margins WRITE setMargins)
    Q_PROPERTY(QMargins minimumMargins READ minimumMargins WRITE setMinimumMargins)
    Q_PROPERTY(QSize minimumSize READ minimumSize WRITE setMinimumSize)
    Q_PROPERTY(QSize maximumSize READ maximumSize WRITE setMaximumSize)
    Q_PROPERTY(SizeConstraintRect sizeConstraintRect READ sizeConstraintRect WRITE setSizeConstraintRect)
    /// \endcond
public:
    /*!
    Defines the phases of the update process, that happens just before a replot. At each phase,
    \ref update is called with the according UpdatePhase value.
  */
    enum UpdatePhase { upPreparation ///< Phase used for any type of preparation that needs to be done before margin calculation and layout
                       ,upMargins    ///< Phase in which the margins are calculated and set
                       ,upLayout     ///< Final phase in which the layout system places the rects of the elements
    };
    Q_ENUMS(UpdatePhase)

    /*!
    Defines to which rect of a layout element the size constraints that can be set via \ref
    setMinimumSize and \ref setMaximumSize apply. The outer rect (\ref outerRect) includes the
    margins (e.g. in the case of a QCPAxisRect the axis labels), whereas the inner rect (\ref rect)
    does not.

    \see setSizeConstraintRect
  */
    enum SizeConstraintRect { scrInnerRect ///< Minimum/Maximum size constraints apply to inner rect
                              , scrOuterRect ///< Minimum/Maximum size constraints apply to outer rect, thus include layout element margins
    };
    Q_ENUMS(SizeConstraintRect)

    explicit QCPLayoutElement(QCustomPlot *parentPlot=nullptr);
    virtual ~QCPLayoutElement() Q_DECL_OVERRIDE;

    // getters:
    QCPLayout *layout() const { return mParentLayout; }
    QRect rect() const { return mRect; }
    QRect outerRect() const { return mOuterRect; }
    QMargins margins() const { return mMargins; }
    QMargins minimumMargins() const { return mMinimumMargins; }
    QCP::MarginSides autoMargins() const { return mAutoMargins; }
    QSize minimumSize() const { return mMinimumSize; }
    QSize maximumSize() const { return mMaximumSize; }
    SizeConstraintRect sizeConstraintRect() const { return mSizeConstraintRect; }
    QCPMarginGroup *marginGroup(QCP::MarginSide side) const { return mMarginGroups.value(side, nullptr); }
    QHash<QCP::MarginSide, QCPMarginGroup*> marginGroups() const { return mMarginGroups; }

    // setters:
    void setOuterRect(const QRect &rect);
    void setMargins(const QMargins &margins);
    void setMinimumMargins(const QMargins &margins);
    void setAutoMargins(QCP::MarginSides sides);
    void setMinimumSize(const QSize &size);
    void setMinimumSize(int width, int height);
    void setMaximumSize(const QSize &size);
    void setMaximumSize(int width, int height);
    void setSizeConstraintRect(SizeConstraintRect constraintRect);
    void setMarginGroup(QCP::MarginSides sides, QCPMarginGroup *group);

    // introduced virtual methods:
    virtual void update(UpdatePhase phase);
    virtual QSize minimumOuterSizeHint() const;
    virtual QSize maximumOuterSizeHint() const;
    virtual QList<QCPLayoutElement*> elements(bool recursive) const;

    // reimplemented virtual methods:
    virtual double selectTest(const QPointF &pos, bool onlySelectable, QVariant *details=nullptr) const Q_DECL_OVERRIDE;

protected:
    // property members:
    QCPLayout *mParentLayout;
    QSize mMinimumSize, mMaximumSize;
    SizeConstraintRect mSizeConstraintRect;
    QRect mRect, mOuterRect;
    QMargins mMargins, mMinimumMargins;
    QCP::MarginSides mAutoMargins;
    QHash<QCP::MarginSide, QCPMarginGroup*> mMarginGroups;

    // introduced virtual methods:
    virtual int calculateAutoMargin(QCP::MarginSide side);
    virtual void layoutChanged();

    // reimplemented virtual methods:
    virtual void applyDefaultAntialiasingHint(QCPPainter *painter) const Q_DECL_OVERRIDE { Q_UNUSED(painter) }
    virtual void draw(QCPPainter *painter) Q_DECL_OVERRIDE { Q_UNUSED(painter) }
    virtual void parentPlotInitialized(QCustomPlot *parentPlot) Q_DECL_OVERRIDE;

private:
    Q_DISABLE_COPY(QCPLayoutElement)

    friend class QCustomPlot;
    friend class QCPLayout;
    friend class QCPMarginGroup;
};
Q_DECLARE_METATYPE(QCPLayoutElement::UpdatePhase)


class QCP_LIB_DECL QCPLayout : public QCPLayoutElement
{
    Q_OBJECT
public:
    explicit QCPLayout();

    // reimplemented virtual methods:
    virtual void update(UpdatePhase phase) Q_DECL_OVERRIDE;
    virtual QList<QCPLayoutElement*> elements(bool recursive) const Q_DECL_OVERRIDE;

    // introduced virtual methods:
    virtual int elementCount() const = 0;
    virtual QCPLayoutElement* elementAt(int index) const = 0;
    virtual QCPLayoutElement* takeAt(int index) = 0;
    virtual bool take(QCPLayoutElement* element) = 0;
    virtual void simplify();

    // non-virtual methods:
    bool removeAt(int index);
    bool remove(QCPLayoutElement* element);
    void clear();

protected:
    // introduced virtual methods:
    virtual void updateLayout();

    // non-virtual methods:
    void sizeConstraintsChanged() const;
    void adoptElement(QCPLayoutElement *el);
    void releaseElement(QCPLayoutElement *el);
    QVector<int> getSectionSizes(QVector<int> maxSizes, QVector<int> minSizes, QVector<double> stretchFactors, int totalSize) const;
    static QSize getFinalMinimumOuterSize(const QCPLayoutElement *el);
    static QSize getFinalMaximumOuterSize(const QCPLayoutElement *el);

private:
    Q_DISABLE_COPY(QCPLayout)
    friend class QCPLayoutElement;
};


class QCP_LIB_DECL QCPLayoutGrid : public QCPLayout
{
    Q_OBJECT
    /// \cond INCLUDE_QPROPERTIES
    Q_PROPERTY(int rowCount READ rowCount)
    Q_PROPERTY(int columnCount READ columnCount)
    Q_PROPERTY(QList<double> columnStretchFactors READ columnStretchFactors WRITE setColumnStretchFactors)
    Q_PROPERTY(QList<double> rowStretchFactors READ rowStretchFactors WRITE setRowStretchFactors)
    Q_PROPERTY(int columnSpacing READ columnSpacing WRITE setColumnSpacing)
    Q_PROPERTY(int rowSpacing READ rowSpacing WRITE setRowSpacing)
    Q_PROPERTY(FillOrder fillOrder READ fillOrder WRITE setFillOrder)
    Q_PROPERTY(int wrap READ wrap WRITE setWrap)
    /// \endcond
public:

    /*!
    Defines in which direction the grid is filled when using \ref addElement(QCPLayoutElement*).
    The column/row at which wrapping into the next row/column occurs can be specified with \ref
    setWrap.

    \see setFillOrder
  */
    enum FillOrder { foRowsFirst    ///< Rows are filled first, and a new element is wrapped to the next column if the row count would exceed \ref setWrap.
                     ,foColumnsFirst ///< Columns are filled first, and a new element is wrapped to the next row if the column count would exceed \ref setWrap.
    };
    Q_ENUMS(FillOrder)

    explicit QCPLayoutGrid();
    virtual ~QCPLayoutGrid() Q_DECL_OVERRIDE;

    // getters:
    int rowCount() const { return mElements.size(); }
    int columnCount() const { return mElements.size() > 0 ? mElements.first().size() : 0; }
    QList<double> columnStretchFactors() const { return mColumnStretchFactors; }
    QList<double> rowStretchFactors() const { return mRowStretchFactors; }
    int columnSpacing() const { return mColumnSpacing; }
    int rowSpacing() const { return mRowSpacing; }
    int wrap() const { return mWrap; }
    FillOrder fillOrder() const { return mFillOrder; }

    // setters:
    void setColumnStretchFactor(int column, double factor);
    void setColumnStretchFactors(const QList<double> &factors);
    void setRowStretchFactor(int row, double factor);
    void setRowStretchFactors(const QList<double> &factors);
    void setColumnSpacing(int pixels);
    void setRowSpacing(int pixels);
    void setWrap(int count);
    void setFillOrder(FillOrder order, bool rearrange=true);

    // reimplemented virtual methods:
    virtual void updateLayout() Q_DECL_OVERRIDE;
    virtual int elementCount() const Q_DECL_OVERRIDE { return rowCount()*columnCount(); }
    virtual QCPLayoutElement* elementAt(int index) const Q_DECL_OVERRIDE;
    virtual QCPLayoutElement* takeAt(int index) Q_DECL_OVERRIDE;
    virtual bool take(QCPLayoutElement* element) Q_DECL_OVERRIDE;
    virtual QList<QCPLayoutElement*> elements(bool recursive) const Q_DECL_OVERRIDE;
    virtual void simplify() Q_DECL_OVERRIDE;
    virtual QSize minimumOuterSizeHint() const Q_DECL_OVERRIDE;
    virtual QSize maximumOuterSizeHint() const Q_DECL_OVERRIDE;

    // non-virtual methods:
    QCPLayoutElement *element(int row, int column) const;
    bool addElement(int row, int column, QCPLayoutElement *element);
    bool addElement(QCPLayoutElement *element);
    bool hasElement(int row, int column);
    void expandTo(int newRowCount, int newColumnCount);
    void insertRow(int newIndex);
    void insertColumn(int newIndex);
    int rowColToIndex(int row, int column) const;
    void indexToRowCol(int index, int &row, int &column) const;

protected:
    // property members:
    QList<QList<QCPLayoutElement*> > mElements;
    QList<double> mColumnStretchFactors;
    QList<double> mRowStretchFactors;
    int mColumnSpacing, mRowSpacing;
    int mWrap;
    FillOrder mFillOrder;

    // non-virtual methods:
    void getMinimumRowColSizes(QVector<int> *minColWidths, QVector<int> *minRowHeights) const;
    void getMaximumRowColSizes(QVector<int> *maxColWidths, QVector<int> *maxRowHeights) const;

private:
    Q_DISABLE_COPY(QCPLayoutGrid)
};
Q_DECLARE_METATYPE(QCPLayoutGrid::FillOrder)


class QCP_LIB_DECL QCPLayoutInset : public QCPLayout
{
    Q_OBJECT
public:
    /*!
    Defines how the placement and sizing is handled for a certain element in a QCPLayoutInset.
  */
    enum InsetPlacement { ipFree            ///< The element may be positioned/sized arbitrarily, see \ref setInsetRect
                          ,ipBorderAligned  ///< The element is aligned to one of the layout sides, see \ref setInsetAlignment
    };
    Q_ENUMS(InsetPlacement)

    explicit QCPLayoutInset();
    virtual ~QCPLayoutInset() Q_DECL_OVERRIDE;

    // getters:
    InsetPlacement insetPlacement(int index) const;
    Qt::Alignment insetAlignment(int index) const;
    QRectF insetRect(int index) const;

    // setters:
    void setInsetPlacement(int index, InsetPlacement placement);
    void setInsetAlignment(int index, Qt::Alignment alignment);
    void setInsetRect(int index, const QRectF &rect);

    // reimplemented virtual methods:
    virtual void updateLayout() Q_DECL_OVERRIDE;
    virtual int elementCount() const Q_DECL_OVERRIDE;
    virtual QCPLayoutElement* elementAt(int index) const Q_DECL_OVERRIDE;
    virtual QCPLayoutElement* takeAt(int index) Q_DECL_OVERRIDE;
    virtual bool take(QCPLayoutElement* element) Q_DECL_OVERRIDE;
    virtual void simplify() Q_DECL_OVERRIDE {}
    virtual double selectTest(const QPointF &pos, bool onlySelectable, QVariant *details=nullptr) const Q_DECL_OVERRIDE;

    // non-virtual methods:
    void addElement(QCPLayoutElement *element, Qt::Alignment alignment);
    void addElement(QCPLayoutElement *element, const QRectF &rect);

protected:
    // property members:
    QList<QCPLayoutElement*> mElements;
    QList<InsetPlacement> mInsetPlacement;
    QList<Qt::Alignment> mInsetAlignment;
    QList<QRectF> mInsetRect;

private:
    Q_DISABLE_COPY(QCPLayoutInset)
};
Q_DECLARE_METATYPE(QCPLayoutInset::InsetPlacement)

/* end of 'src/layout.h' */


/* including file 'src/lineending.h'       */
/* modified 2021-03-29T02:30:44, size 4426 */

class QCP_LIB_DECL QCPLineEnding
{
    Q_GADGET
public:
    /*!
    Defines the type of ending decoration for line-like items, e.g. an arrow.

    \image html QCPLineEnding.png

    The width and length of these decorations can be controlled with the functions \ref setWidth
    and \ref setLength. Some decorations like \ref esDisc, \ref esSquare, \ref esDiamond and \ref esBar only
    support a width, the length property is ignored.

    \see QCPItemLine::setHead, QCPItemLine::setTail, QCPItemCurve::setHead, QCPItemCurve::setTail, QCPAxis::setLowerEnding, QCPAxis::setUpperEnding
  */
    enum EndingStyle { esNone          ///< No ending decoration
                       ,esFlatArrow    ///< A filled arrow head with a straight/flat back (a triangle)
                       ,esSpikeArrow   ///< A filled arrow head with an indented back
                       ,esLineArrow    ///< A non-filled arrow head with open back
                       ,esDisc         ///< A filled circle
                       ,esSquare       ///< A filled square
                       ,esDiamond      ///< A filled diamond (45 degrees rotated square)
                       ,esBar          ///< A bar perpendicular to the line
                       ,esHalfBar      ///< A bar perpendicular to the line, pointing out to only one side (to which side can be changed with \ref setInverted)
                       ,esSkewedBar    ///< A bar that is skewed (skew controllable via \ref setLength)
    };
    Q_ENUMS(EndingStyle)

    QCPLineEnding();
    QCPLineEnding(EndingStyle style, double width=8, double length=10, bool inverted=false);

    // getters:
    EndingStyle style() const { return mStyle; }
    double width() const { return mWidth; }
    double length() const { return mLength; }
    bool inverted() const { return mInverted; }

    // setters:
    void setStyle(EndingStyle style);
    void setWidth(double width);
    void setLength(double length);
    void setInverted(bool inverted);

    // non-property methods:
    double boundingDistance() const;
    double realLength() const;
    void draw(QCPPainter *painter, const QCPVector2D &pos, const QCPVector2D &dir) const;
    void draw(QCPPainter *painter, const QCPVector2D &pos, double angle) const;

protected:
    // property members:
    EndingStyle mStyle;
    double mWidth, mLength;
    bool mInverted;
};
Q_DECLARE_TYPEINFO(QCPLineEnding, Q_MOVABLE_TYPE);
Q_DECLARE_METATYPE(QCPLineEnding::EndingStyle)

/* end of 'src/lineending.h' */


/* including file 'src/axis/labelpainter.h' */
/* modified 2021-03-29T02:30:44, size 7086  */

class QCPLabelPainterPrivate
{
    Q_GADGET
public:
    /*!
    TODO
  */
    enum AnchorMode { amRectangular    ///<
                      ,amSkewedUpright ///<
                      ,amSkewedRotated ///<
    };
    Q_ENUMS(AnchorMode)

    /*!
    TODO
  */
    enum AnchorReferenceType { artNormal    ///<
                               ,artTangent ///<
    };
    Q_ENUMS(AnchorReferenceType)

    /*!
    TODO
  */
    enum AnchorSide { asLeft      ///<
                      ,asRight    ///<
                      ,asTop      ///<
                      ,asBottom   ///<
                      ,asTopLeft
                      ,asTopRight
                      ,asBottomRight
                      ,asBottomLeft
    };
    Q_ENUMS(AnchorSide)

    explicit QCPLabelPainterPrivate(QCustomPlot *parentPlot);
    virtual ~QCPLabelPainterPrivate();

    // setters:
    void setAnchorSide(AnchorSide side);
    void setAnchorMode(AnchorMode mode);
    void setAnchorReference(const QPointF &pixelPoint);
    void setAnchorReferenceType(AnchorReferenceType type);
    void setFont(const QFont &font);
    void setColor(const QColor &color);
    void setPadding(int padding);
    void setRotation(double rotation);
    void setSubstituteExponent(bool enabled);
    void setMultiplicationSymbol(QChar symbol);
    void setAbbreviateDecimalPowers(bool enabled);
    void setCacheSize(int labelCount);

    // getters:
    AnchorMode anchorMode() const { return mAnchorMode; }
    AnchorSide anchorSide() const { return mAnchorSide; }
    QPointF anchorReference() const { return mAnchorReference; }
    AnchorReferenceType anchorReferenceType() const { return mAnchorReferenceType; }
    QFont font() const { return mFont; }
    QColor color() const { return mColor; }
    int padding() const { return mPadding; }
    double rotation() const { return mRotation; }
    bool substituteExponent() const { return mSubstituteExponent; }
    QChar multiplicationSymbol() const { return mMultiplicationSymbol; }
    bool abbreviateDecimalPowers() const { return mAbbreviateDecimalPowers; }
    int cacheSize() const;

    //virtual int size() const;

    // non-property methods:
    void drawTickLabel(QCPPainter *painter, const QPointF &tickPos, const QString &text);
    void clearCache();

    // constants that may be used with setMultiplicationSymbol:
    static const QChar SymbolDot;
    static const QChar SymbolCross;

protected:
    struct CachedLabel
    {
        QPoint offset;
        QPixmap pixmap;
    };
    struct LabelData
    {
        AnchorSide side;
        double rotation; // angle in degrees
        QTransform transform; // the transform about the label anchor which is at (0, 0). Does not contain final absolute x/y positioning on the plot/axis
        QString basePart, expPart, suffixPart;
        QRect baseBounds, expBounds, suffixBounds;
        QRect totalBounds; // is in a coordinate system where label top left is at (0, 0)
        QRect rotatedTotalBounds; // is in a coordinate system where the label anchor is at (0, 0)
        QFont baseFont, expFont;
        QColor color;
    };

    // property members:
    AnchorMode mAnchorMode;
    AnchorSide mAnchorSide;
    QPointF mAnchorReference;
    AnchorReferenceType mAnchorReferenceType;
    QFont mFont;
    QColor mColor;
    int mPadding;
    double mRotation; // this is the rotation applied uniformly to all labels, not the heterogeneous rotation in amCircularRotated mode
    bool mSubstituteExponent;
    QChar mMultiplicationSymbol;
    bool mAbbreviateDecimalPowers;
    // non-property members:
    QCustomPlot *mParentPlot;
    QByteArray mLabelParameterHash; // to determine whether mLabelCache needs to be cleared due to changed parameters
    QCache<QString, CachedLabel> mLabelCache;
    QRect mAxisSelectionBox, mTickLabelsSelectionBox, mLabelSelectionBox;
    int mLetterCapHeight, mLetterDescent;

    // introduced virtual methods:
    virtual void drawLabelMaybeCached(QCPPainter *painter, const QFont &font, const QColor &color, const QPointF &pos, AnchorSide side, double rotation, const QString &text);
    virtual QByteArray generateLabelParameterHash() const; // TODO: get rid of this in favor of invalidation flag upon setters?

    // non-virtual methods:
    QPointF getAnchorPos(const QPointF &tickPos);
    void drawText(QCPPainter *painter, const QPointF &pos, const LabelData &labelData) const;
    LabelData getTickLabelData(const QFont &font, const QColor &color, double rotation, AnchorSide side, const QString &text) const;
    void applyAnchorTransform(LabelData &labelData) const;
    //void getMaxTickLabelSize(const QFont &font, const QString &text, QSize *tickLabelsSize) const;
    CachedLabel *createCachedLabel(const LabelData &labelData) const;
    QByteArray cacheKey(const QString &text, const QColor &color, double rotation, AnchorSide side) const;
    AnchorSide skewedAnchorSide(const QPointF &tickPos, double sideExpandHorz, double sideExpandVert) const;
    AnchorSide rotationCorrectedSide(AnchorSide side, double rotation) const;
    void analyzeFontMetrics();
};
Q_DECLARE_METATYPE(QCPLabelPainterPrivate::AnchorMode)
Q_DECLARE_METATYPE(QCPLabelPainterPrivate::AnchorSide)


/* end of 'src/axis/labelpainter.h' */


/* including file 'src/axis/axisticker.h'  */
/* modified 2021-03-29T02:30:44, size 4230 */

class QCP_LIB_DECL QCPAxisTicker
{
    Q_GADGET
public:
    /*!
    Defines the strategies that the axis ticker may follow when choosing the size of the tick step.

    \see setTickStepStrategy
  */
    enum TickStepStrategy
    {
        tssReadability    ///< A nicely readable tick step is prioritized over matching the requested number of ticks (see \ref setTickCount)
        ,tssMeetTickCount ///< Less readable tick steps are allowed which in turn facilitates getting closer to the requested tick count
    };
    Q_ENUMS(TickStepStrategy)

    QCPAxisTicker();
    virtual ~QCPAxisTicker();

    // getters:
    TickStepStrategy tickStepStrategy() const { return mTickStepStrategy; }
    int tickCount() const { return mTickCount; }
    double tickOrigin() const { return mTickOrigin; }

    // setters:
    void setTickStepStrategy(TickStepStrategy strategy);
    void setTickCount(int count);
    void setTickOrigin(double origin);

    // introduced virtual methods:
    virtual void generate(const QCPRange &range, const QLocale &locale, QChar formatChar, int precision, QVector<double> &ticks, QVector<double> *subTicks, QVector<QString> *tickLabels);

protected:
    // property members:
    TickStepStrategy mTickStepStrategy;
    int mTickCount;
    double mTickOrigin;

    // introduced virtual methods:
    virtual double getTickStep(const QCPRange &range);
    virtual int getSubTickCount(double tickStep);
    virtual QString getTickLabel(double tick, const QLocale &locale, QChar formatChar, int precision);
    virtual QVector<double> createTickVector(double tickStep, const QCPRange &range);
    virtual QVector<double> createSubTickVector(int subTickCount, const QVector<double> &ticks);
    virtual QVector<QString> createLabelVector(const QVector<double> &ticks, const QLocale &locale, QChar formatChar, int precision);

    // non-virtual methods:
    void trimTicks(const QCPRange &range, QVector<double> &ticks, bool keepOneOutlier) const;
    double pickClosest(double target, const QVector<double> &candidates) const;
    double getMantissa(double input, double *magnitude=nullptr) const;
    double cleanMantissa(double input) const;

private:
    Q_DISABLE_COPY(QCPAxisTicker)

};
Q_DECLARE_METATYPE(QCPAxisTicker::TickStepStrategy)
Q_DECLARE_METATYPE(QSharedPointer<QCPAxisTicker>)

/* end of 'src/axis/axisticker.h' */


/* including file 'src/axis/axistickerdatetime.h' */
/* modified 2021-03-29T02:30:44, size 3600        */

class QCP_LIB_DECL QCPAxisTickerDateTime : public QCPAxisTicker
{
public:
    QCPAxisTickerDateTime();

    // getters:
    QString dateTimeFormat() const { return mDateTimeFormat; }
    Qt::TimeSpec dateTimeSpec() const { return mDateTimeSpec; }
# if QT_VERSION >= QT_VERSION_CHECK(5, 2, 0)
    QTimeZone timeZone() const { return mTimeZone; }
#endif

    // setters:
    void setDateTimeFormat(const QString &format);
    void setDateTimeSpec(Qt::TimeSpec spec);
# if QT_VERSION >= QT_VERSION_CHECK(5, 2, 0)
    void setTimeZone(const QTimeZone &zone);
# endif
    void setTickOrigin(double origin); // hides base class method but calls baseclass implementation ("using" throws off IDEs and doxygen)
    void setTickOrigin(const QDateTime &origin);

    // static methods:
    static QDateTime keyToDateTime(double key);
    static double dateTimeToKey(const QDateTime &dateTime);
    static double dateTimeToKey(const QDate &date, Qt::TimeSpec timeSpec=Qt::LocalTime);

protected:
    // property members:
    QString mDateTimeFormat;
    Qt::TimeSpec mDateTimeSpec;
# if QT_VERSION >= QT_VERSION_CHECK(5, 2, 0)
    QTimeZone mTimeZone;
# endif
    // non-property members:
    enum DateStrategy {dsNone, dsUniformTimeInDay, dsUniformDayInMonth} mDateStrategy;

    // reimplemented virtual methods:
    virtual double getTickStep(const QCPRange &range) Q_DECL_OVERRIDE;
    virtual int getSubTickCount(double tickStep) Q_DECL_OVERRIDE;
    virtual QString getTickLabel(double tick, const QLocale &locale, QChar formatChar, int precision) Q_DECL_OVERRIDE;
    virtual QVector<double> createTickVector(double tickStep, const QCPRange &range) Q_DECL_OVERRIDE;
};

/* end of 'src/axis/axistickerdatetime.h' */


/* including file 'src/axis/axistickertime.h' */
/* modified 2021-03-29T02:30:44, size 3542    */

class QCP_LIB_DECL QCPAxisTickerTime : public QCPAxisTicker
{
    Q_GADGET
public:
    /*!
    Defines the logical units in which fractions of time spans can be expressed.

    \see setFieldWidth, setTimeFormat
  */
    enum TimeUnit { tuMilliseconds ///< Milliseconds, one thousandth of a second (%%z in \ref setTimeFormat)
                    ,tuSeconds     ///< Seconds (%%s in \ref setTimeFormat)
                    ,tuMinutes     ///< Minutes (%%m in \ref setTimeFormat)
                    ,tuHours       ///< Hours (%%h in \ref setTimeFormat)
                    ,tuDays        ///< Days (%%d in \ref setTimeFormat)
    };
    Q_ENUMS(TimeUnit)

    QCPAxisTickerTime();

    // getters:
    QString timeFormat() const { return mTimeFormat; }
    int fieldWidth(TimeUnit unit) const { return mFieldWidth.value(unit); }

    // setters:
    void setTimeFormat(const QString &format);
    void setFieldWidth(TimeUnit unit, int width);

protected:
    // property members:
    QString mTimeFormat;
    QHash<TimeUnit, int> mFieldWidth;

    // non-property members:
    TimeUnit mSmallestUnit, mBiggestUnit;
    QHash<TimeUnit, QString> mFormatPattern;

    // reimplemented virtual methods:
    virtual double getTickStep(const QCPRange &range) Q_DECL_OVERRIDE;
    virtual int getSubTickCount(double tickStep) Q_DECL_OVERRIDE;
    virtual QString getTickLabel(double tick, const QLocale &locale, QChar formatChar, int precision) Q_DECL_OVERRIDE;

    // non-virtual methods:
    void replaceUnit(QString &text, TimeUnit unit, int value) const;
};
Q_DECLARE_METATYPE(QCPAxisTickerTime::TimeUnit)

/* end of 'src/axis/axistickertime.h' */


/* including file 'src/axis/axistickerfixed.h' */
/* modified 2021-03-29T02:30:44, size 3308     */

class QCP_LIB_DECL QCPAxisTickerFixed : public QCPAxisTicker
{
    Q_GADGET
public:
    /*!
    Defines how the axis ticker may modify the specified tick step (\ref setTickStep) in order to
    control the number of ticks in the axis range.

    \see setScaleStrategy
  */
    enum ScaleStrategy { ssNone      ///< Modifications are not allowed, the specified tick step is absolutely fixed. This might cause a high tick density and overlapping labels if the axis range is zoomed out.
                         ,ssMultiples ///< An integer multiple of the specified tick step is allowed. The used factor follows the base class properties of \ref setTickStepStrategy and \ref setTickCount.
                         ,ssPowers    ///< An integer power of the specified tick step is allowed.
    };
    Q_ENUMS(ScaleStrategy)

    QCPAxisTickerFixed();

    // getters:
    double tickStep() const { return mTickStep; }
    ScaleStrategy scaleStrategy() const { return mScaleStrategy; }

    // setters:
    void setTickStep(double step);
    void setScaleStrategy(ScaleStrategy strategy);

protected:
    // property members:
    double mTickStep;
    ScaleStrategy mScaleStrategy;

    // reimplemented virtual methods:
    virtual double getTickStep(const QCPRange &range) Q_DECL_OVERRIDE;
};
Q_DECLARE_METATYPE(QCPAxisTickerFixed::ScaleStrategy)

/* end of 'src/axis/axistickerfixed.h' */


/* including file 'src/axis/axistickertext.h' */
/* modified 2021-03-29T02:30:44, size 3090    */

class QCP_LIB_DECL QCPAxisTickerText : public QCPAxisTicker
{
public:
    QCPAxisTickerText();

    // getters:
    QMap<double, QString> &ticks() { return mTicks; }
    int subTickCount() const { return mSubTickCount; }

    // setters:
    void setTicks(const QMap<double, QString> &ticks);
    void setTicks(const QVector<double> &positions, const QVector<QString> &labels);
    void setSubTickCount(int subTicks);

    // non-virtual methods:
    void clear();
    void addTick(double position, const QString &label);
    void addTicks(const QMap<double, QString> &ticks);
    void addTicks(const QVector<double> &positions, const QVector<QString> &labels);

protected:
    // property members:
    QMap<double, QString> mTicks;
    int mSubTickCount;

    // reimplemented virtual methods:
    virtual double getTickStep(const QCPRange &range) Q_DECL_OVERRIDE;
    virtual int getSubTickCount(double tickStep) Q_DECL_OVERRIDE;
    virtual QString getTickLabel(double tick, const QLocale &locale, QChar formatChar, int precision) Q_DECL_OVERRIDE;
    virtual QVector<double> createTickVector(double tickStep, const QCPRange &range) Q_DECL_OVERRIDE;
};

/* end of 'src/axis/axistickertext.h' */


/* including file 'src/axis/axistickerpi.h' */
/* modified 2021-03-29T02:30:44, size 3911  */

class QCP_LIB_DECL QCPAxisTickerPi : public QCPAxisTicker
{
    Q_GADGET
public:
    /*!
    Defines how fractions should be displayed in tick labels.

    \see setFractionStyle
  */
    enum FractionStyle { fsFloatingPoint     ///< Fractions are displayed as regular decimal floating point numbers, e.g. "0.25" or "0.125".
                         ,fsAsciiFractions   ///< Fractions are written as rationals using ASCII characters only, e.g. "1/4" or "1/8"
                         ,fsUnicodeFractions ///< Fractions are written using sub- and superscript UTF-8 digits and the fraction symbol.
    };
    Q_ENUMS(FractionStyle)

    QCPAxisTickerPi();

    // getters:
    QString piSymbol() const { return mPiSymbol; }
    double piValue() const { return mPiValue; }
    bool periodicity() const { return mPeriodicity; }
    FractionStyle fractionStyle() const { return mFractionStyle; }

    // setters:
    void setPiSymbol(QString symbol);
    void setPiValue(double pi);
    void setPeriodicity(int multiplesOfPi);
    void setFractionStyle(FractionStyle style);

protected:
    // property members:
    QString mPiSymbol;
    double mPiValue;
    int mPeriodicity;
    FractionStyle mFractionStyle;

    // non-property members:
    double mPiTickStep; // size of one tick step in units of mPiValue

    // reimplemented virtual methods:
    virtual double getTickStep(const QCPRange &range) Q_DECL_OVERRIDE;
    virtual int getSubTickCount(double tickStep) Q_DECL_OVERRIDE;
    virtual QString getTickLabel(double tick, const QLocale &locale, QChar formatChar, int precision) Q_DECL_OVERRIDE;

    // non-virtual methods:
    void simplifyFraction(int &numerator, int &denominator) const;
    QString fractionToString(int numerator, int denominator) const;
    QString unicodeFraction(int numerator, int denominator) const;
    QString unicodeSuperscript(int number) const;
    QString unicodeSubscript(int number) const;
};
Q_DECLARE_METATYPE(QCPAxisTickerPi::FractionStyle)

/* end of 'src/axis/axistickerpi.h' */


/* including file 'src/axis/axistickerlog.h' */
/* modified 2021-03-29T02:30:44, size 2594   */

class QCP_LIB_DECL QCPAxisTickerLog : public QCPAxisTicker
{
public:
    QCPAxisTickerLog();

    // getters:
    double logBase() const { return mLogBase; }
    int subTickCount() const { return mSubTickCount; }

    // setters:
    void setLogBase(double base);
    void setSubTickCount(int subTicks);

protected:
    // property members:
    double mLogBase;
    int mSubTickCount;

    // non-property members:
    double mLogBaseLnInv;

    // reimplemented virtual methods:
    virtual int getSubTickCount(double tickStep) Q_DECL_OVERRIDE;
    virtual QVector<double> createTickVector(double tickStep, const QCPRange &range) Q_DECL_OVERRIDE;
};

/* end of 'src/axis/axistickerlog.h' */


/* including file 'src/axis/axis.h'         */
/* modified 2021-03-29T02:30:44, size 20913 */

class QCP_LIB_DECL QCPGrid :public QCPLayerable
{
    Q_OBJECT
    /// \cond INCLUDE_QPROPERTIES
    Q_PROPERTY(bool subGridVisible READ subGridVisible WRITE setSubGridVisible)
    Q_PROPERTY(bool antialiasedSubGrid READ antialiasedSubGrid WRITE setAntialiasedSubGrid)
    Q_PROPERTY(bool antialiasedZeroLine READ antialiasedZeroLine WRITE setAntialiasedZeroLine)
    Q_PROPERTY(QPen pen READ pen WRITE setPen)
    Q_PROPERTY(QPen subGridPen READ subGridPen WRITE setSubGridPen)
    Q_PROPERTY(QPen zeroLinePen READ zeroLinePen WRITE setZeroLinePen)
    /// \endcond
public:
    explicit QCPGrid(QCPAxis *parentAxis);

    // getters:
    bool subGridVisible() const { return mSubGridVisible; }
    bool antialiasedSubGrid() const { return mAntialiasedSubGrid; }
    bool antialiasedZeroLine() const { return mAntialiasedZeroLine; }
    QPen pen() const { return mPen; }
    QPen subGridPen() const { return mSubGridPen; }
    QPen zeroLinePen() const { return mZeroLinePen; }

    // setters:
    void setSubGridVisible(bool visible);
    void setAntialiasedSubGrid(bool enabled);
    void setAntialiasedZeroLine(bool enabled);
    void setPen(const QPen &pen);
    void setSubGridPen(const QPen &pen);
    void setZeroLinePen(const QPen &pen);

protected:
    // property members:
    bool mSubGridVisible;
    bool mAntialiasedSubGrid, mAntialiasedZeroLine;
    QPen mPen, mSubGridPen, mZeroLinePen;

    // non-property members:
    QCPAxis *mParentAxis;

    // reimplemented virtual methods:
    virtual void applyDefaultAntialiasingHint(QCPPainter *painter) const Q_DECL_OVERRIDE;
    virtual void draw(QCPPainter *painter) Q_DECL_OVERRIDE;

    // non-virtual methods:
    void drawGridLines(QCPPainter *painter) const;
    void drawSubGridLines(QCPPainter *painter) const;

    friend class QCPAxis;
};


class QCP_LIB_DECL QCPAxis : public QCPLayerable
{
    Q_OBJECT
    /// \cond INCLUDE_QPROPERTIES
    Q_PROPERTY(AxisType axisType READ axisType)
    Q_PROPERTY(QCPAxisRect* axisRect READ axisRect)
    Q_PROPERTY(ScaleType scaleType READ scaleType WRITE setScaleType NOTIFY scaleTypeChanged)
    Q_PROPERTY(QCPRange range READ range WRITE setRange NOTIFY rangeChanged)
    Q_PROPERTY(bool rangeReversed READ rangeReversed WRITE setRangeReversed)
    Q_PROPERTY(QSharedPointer<QCPAxisTicker> ticker READ ticker WRITE setTicker)
    Q_PROPERTY(bool ticks READ ticks WRITE setTicks)
    Q_PROPERTY(bool tickLabels READ tickLabels WRITE setTickLabels)
    Q_PROPERTY(int tickLabelPadding READ tickLabelPadding WRITE setTickLabelPadding)
    Q_PROPERTY(QFont tickLabelFont READ tickLabelFont WRITE setTickLabelFont)
    Q_PROPERTY(QColor tickLabelColor READ tickLabelColor WRITE setTickLabelColor)
    Q_PROPERTY(double tickLabelRotation READ tickLabelRotation WRITE setTickLabelRotation)
    Q_PROPERTY(LabelSide tickLabelSide READ tickLabelSide WRITE setTickLabelSide)
    Q_PROPERTY(QString numberFormat READ numberFormat WRITE setNumberFormat)
    Q_PROPERTY(int numberPrecision READ numberPrecision WRITE setNumberPrecision)
    Q_PROPERTY(QVector<double> tickVector READ tickVector)
    Q_PROPERTY(QVector<QString> tickVectorLabels READ tickVectorLabels)
    Q_PROPERTY(int tickLengthIn READ tickLengthIn WRITE setTickLengthIn)
    Q_PROPERTY(int tickLengthOut READ tickLengthOut WRITE setTickLengthOut)
    Q_PROPERTY(bool subTicks READ subTicks WRITE setSubTicks)
    Q_PROPERTY(int subTickLengthIn READ subTickLengthIn WRITE setSubTickLengthIn)
    Q_PROPERTY(int subTickLengthOut READ subTickLengthOut WRITE setSubTickLengthOut)
    Q_PROPERTY(QPen basePen READ basePen WRITE setBasePen)
    Q_PROPERTY(QPen tickPen READ tickPen WRITE setTickPen)
    Q_PROPERTY(QPen subTickPen READ subTickPen WRITE setSubTickPen)
    Q_PROPERTY(QFont labelFont READ labelFont WRITE setLabelFont)
    Q_PROPERTY(QColor labelColor READ labelColor WRITE setLabelColor)
    Q_PROPERTY(QString label READ label WRITE setLabel)
    Q_PROPERTY(int labelPadding READ labelPadding WRITE setLabelPadding)
    Q_PROPERTY(int padding READ padding WRITE setPadding)
    Q_PROPERTY(int offset READ offset WRITE setOffset)
    Q_PROPERTY(SelectableParts selectedParts READ selectedParts WRITE setSelectedParts NOTIFY selectionChanged)
    Q_PROPERTY(SelectableParts selectableParts READ selectableParts WRITE setSelectableParts NOTIFY selectableChanged)
    Q_PROPERTY(QFont selectedTickLabelFont READ selectedTickLabelFont WRITE setSelectedTickLabelFont)
    Q_PROPERTY(QFont selectedLabelFont READ selectedLabelFont WRITE setSelectedLabelFont)
    Q_PROPERTY(QColor selectedTickLabelColor READ selectedTickLabelColor WRITE setSelectedTickLabelColor)
    Q_PROPERTY(QColor selectedLabelColor READ selectedLabelColor WRITE setSelectedLabelColor)
    Q_PROPERTY(QPen selectedBasePen READ selectedBasePen WRITE setSelectedBasePen)
    Q_PROPERTY(QPen selectedTickPen READ selectedTickPen WRITE setSelectedTickPen)
    Q_PROPERTY(QPen selectedSubTickPen READ selectedSubTickPen WRITE setSelectedSubTickPen)
    Q_PROPERTY(QCPLineEnding lowerEnding READ lowerEnding WRITE setLowerEnding)
    Q_PROPERTY(QCPLineEnding upperEnding READ upperEnding WRITE setUpperEnding)
    Q_PROPERTY(QCPGrid* grid READ grid)
    /// \endcond
public:
    /*!
    Defines at which side of the axis rect the axis will appear. This also affects how the tick
    marks are drawn, on which side the labels are placed etc.
  */
    enum AxisType { atLeft    = 0x01  ///< <tt>0x01</tt> Axis is vertical and on the left side of the axis rect
                    ,atRight  = 0x02  ///< <tt>0x02</tt> Axis is vertical and on the right side of the axis rect
                    ,atTop    = 0x04  ///< <tt>0x04</tt> Axis is horizontal and on the top side of the axis rect
                    ,atBottom = 0x08  ///< <tt>0x08</tt> Axis is horizontal and on the bottom side of the axis rect
    };
    Q_ENUMS(AxisType)
    Q_FLAGS(AxisTypes)
    Q_DECLARE_FLAGS(AxisTypes, AxisType)
    /*!
    Defines on which side of the axis the tick labels (numbers) shall appear.

    \see setTickLabelSide
  */
    enum LabelSide { lsInside    ///< Tick labels will be displayed inside the axis rect and clipped to the inner axis rect
                     ,lsOutside  ///< Tick labels will be displayed outside the axis rect
    };
    Q_ENUMS(LabelSide)
    /*!
    Defines the scale of an axis.
    \see setScaleType
  */
    enum ScaleType { stLinear       ///< Linear scaling
                     ,stLogarithmic ///< Logarithmic scaling with correspondingly transformed axis coordinates (possibly also \ref setTicker to a \ref QCPAxisTickerLog instance).
    };
    Q_ENUMS(ScaleType)
    /*!
    Defines the selectable parts of an axis.
    \see setSelectableParts, setSelectedParts
  */
    enum SelectablePart { spNone        = 0      ///< None of the selectable parts
                          ,spAxis       = 0x001  ///< The axis backbone and tick marks
                          ,spTickLabels = 0x002  ///< Tick labels (numbers) of this axis (as a whole, not individually)
                          ,spAxisLabel  = 0x004  ///< The axis label
    };
    Q_ENUMS(SelectablePart)
    Q_FLAGS(SelectableParts)
    Q_DECLARE_FLAGS(SelectableParts, SelectablePart)

    explicit QCPAxis(QCPAxisRect *parent, AxisType type);
    virtual ~QCPAxis() Q_DECL_OVERRIDE;

    // getters:
    AxisType axisType() const { return mAxisType; }
    QCPAxisRect *axisRect() const { return mAxisRect; }
    ScaleType scaleType() const { return mScaleType; }
    const QCPRange range() const { return mRange; }
    bool rangeReversed() const { return mRangeReversed; }
    QSharedPointer<QCPAxisTicker> ticker() const { return mTicker; }
    bool ticks() const { return mTicks; }
    bool tickLabels() const { return mTickLabels; }
    int tickLabelPadding() const;
    QFont tickLabelFont() const { return mTickLabelFont; }
    QColor tickLabelColor() const { return mTickLabelColor; }
    double tickLabelRotation() const;
    LabelSide tickLabelSide() const;
    QString numberFormat() const;
    int numberPrecision() const { return mNumberPrecision; }
    QVector<double> tickVector() const { return mTickVector; }
    QVector<QString> tickVectorLabels() const { return mTickVectorLabels; }
    int tickLengthIn() const;
    int tickLengthOut() const;
    bool subTicks() const { return mSubTicks; }
    int subTickLengthIn() const;
    int subTickLengthOut() const;
    QPen basePen() const { return mBasePen; }
    QPen tickPen() const { return mTickPen; }
    QPen subTickPen() const { return mSubTickPen; }
    QFont labelFont() const { return mLabelFont; }
    QColor labelColor() const { return mLabelColor; }
    QString label() const { return mLabel; }
    int labelPadding() const;
    int padding() const { return mPadding; }
    int offset() const;
    SelectableParts selectedParts() const { return mSelectedParts; }
    SelectableParts selectableParts() const { return mSelectableParts; }
    QFont selectedTickLabelFont() const { return mSelectedTickLabelFont; }
    QFont selectedLabelFont() const { return mSelectedLabelFont; }
    QColor selectedTickLabelColor() const { return mSelectedTickLabelColor; }
    QColor selectedLabelColor() const { return mSelectedLabelColor; }
    QPen selectedBasePen() const { return mSelectedBasePen; }
    QPen selectedTickPen() const { return mSelectedTickPen; }
    QPen selectedSubTickPen() const { return mSelectedSubTickPen; }
    QCPLineEnding lowerEnding() const;
    QCPLineEnding upperEnding() const;
    QCPGrid *grid() const { return mGrid; }

    // setters:
    Q_SLOT void setScaleType(QCPAxis::ScaleType type);
    Q_SLOT void setRange(const QCPRange &range);
    void setRange(double lower, double upper);
    void setRange(double position, double size, Qt::AlignmentFlag alignment);
    void setRangeLower(double lower);
    void setRangeUpper(double upper);
    void setRangeReversed(bool reversed);
    void setTicker(QSharedPointer<QCPAxisTicker> ticker);
    void setTicks(bool show);
    void setTickLabels(bool show);
    void setTickLabelPadding(int padding);
    void setTickLabelFont(const QFont &font);
    void setTickLabelColor(const QColor &color);
    void setTickLabelRotation(double degrees);
    void setTickLabelSide(LabelSide side);
    void setNumberFormat(const QString &formatCode);
    void setNumberPrecision(int precision);
    void setTickLength(int inside, int outside=0);
    void setTickLengthIn(int inside);
    void setTickLengthOut(int outside);
    void setSubTicks(bool show);
    void setSubTickLength(int inside, int outside=0);
    void setSubTickLengthIn(int inside);
    void setSubTickLengthOut(int outside);
    void setBasePen(const QPen &pen);
    void setTickPen(const QPen &pen);
    void setSubTickPen(const QPen &pen);
    void setLabelFont(const QFont &font);
    void setLabelColor(const QColor &color);
    void setLabel(const QString &str);
    void setLabelPadding(int padding);
    void setPadding(int padding);
    void setOffset(int offset);
    void setSelectedTickLabelFont(const QFont &font);
    void setSelectedLabelFont(const QFont &font);
    void setSelectedTickLabelColor(const QColor &color);
    void setSelectedLabelColor(const QColor &color);
    void setSelectedBasePen(const QPen &pen);
    void setSelectedTickPen(const QPen &pen);
    void setSelectedSubTickPen(const QPen &pen);
    Q_SLOT void setSelectableParts(const QCPAxis::SelectableParts &selectableParts);
    Q_SLOT void setSelectedParts(const QCPAxis::SelectableParts &selectedParts);
    void setLowerEnding(const QCPLineEnding &ending);
    void setUpperEnding(const QCPLineEnding &ending);

    // reimplemented virtual methods:
    virtual double selectTest(const QPointF &pos, bool onlySelectable, QVariant *details=nullptr) const Q_DECL_OVERRIDE;

    // non-property methods:
    Qt::Orientation orientation() const { return mOrientation; }
    int pixelOrientation() const { return rangeReversed() != (orientation()==Qt::Vertical) ? -1 : 1; }
    void moveRange(double diff);
    void scaleRange(double factor);
    void scaleRange(double factor, double center);
    void setScaleRatio(const QCPAxis *otherAxis, double ratio=1.0);
    void rescale(bool onlyVisiblePlottables=false);
    double pixelToCoord(double value) const;
    double coordToPixel(double value) const;
    SelectablePart getPartAt(const QPointF &pos) const;
    QList<QCPAbstractPlottable*> plottables() const;
    QList<QCPGraph*> graphs() const;
    QList<QCPAbstractItem*> items() const;

    static AxisType marginSideToAxisType(QCP::MarginSide side);
    static Qt::Orientation orientation(AxisType type) { return type==atBottom || type==atTop ? Qt::Horizontal : Qt::Vertical; }
    static AxisType opposite(AxisType type);

signals:
    void rangeChanged(const QCPRange &newRange);
    void rangeChanged(const QCPRange &newRange, const QCPRange &oldRange);
    void scaleTypeChanged(QCPAxis::ScaleType scaleType);
    void selectionChanged(const QCPAxis::SelectableParts &parts);
    void selectableChanged(const QCPAxis::SelectableParts &parts);

protected:
    // property members:
    // axis base:
    AxisType mAxisType;
    QCPAxisRect *mAxisRect;
    //int mOffset; // in QCPAxisPainter
    int mPadding;
    Qt::Orientation mOrientation;
    SelectableParts mSelectableParts, mSelectedParts;
    QPen mBasePen, mSelectedBasePen;
    //QCPLineEnding mLowerEnding, mUpperEnding; // in QCPAxisPainter
    // axis label:
    //int mLabelPadding; // in QCPAxisPainter
    QString mLabel;
    QFont mLabelFont, mSelectedLabelFont;
    QColor mLabelColor, mSelectedLabelColor;
    // tick labels:
    //int mTickLabelPadding; // in QCPAxisPainter
    bool mTickLabels;
    //double mTickLabelRotation; // in QCPAxisPainter
    QFont mTickLabelFont, mSelectedTickLabelFont;
    QColor mTickLabelColor, mSelectedTickLabelColor;
    int mNumberPrecision;
    QLatin1Char mNumberFormatChar;
    bool mNumberBeautifulPowers;
    //bool mNumberMultiplyCross; // QCPAxisPainter
    // ticks and subticks:
    bool mTicks;
    bool mSubTicks;
    //int mTickLengthIn, mTickLengthOut, mSubTickLengthIn, mSubTickLengthOut; // QCPAxisPainter
    QPen mTickPen, mSelectedTickPen;
    QPen mSubTickPen, mSelectedSubTickPen;
    // scale and range:
    QCPRange mRange;
    bool mRangeReversed;
    ScaleType mScaleType;

    // non-property members:
    QCPGrid *mGrid;
    QCPAxisPainterPrivate *mAxisPainter;
    QSharedPointer<QCPAxisTicker> mTicker;
    QVector<double> mTickVector;
    QVector<QString> mTickVectorLabels;
    QVector<double> mSubTickVector;
    bool mCachedMarginValid;
    int mCachedMargin;
    bool mDragging;
    QCPRange mDragStartRange;
    QCP::AntialiasedElements mAADragBackup, mNotAADragBackup;

    // introduced virtual methods:
    virtual int calculateMargin();

    // reimplemented virtual methods:
    virtual void applyDefaultAntialiasingHint(QCPPainter *painter) const Q_DECL_OVERRIDE;
    virtual void draw(QCPPainter *painter) Q_DECL_OVERRIDE;
    virtual QCP::Interaction selectionCategory() const Q_DECL_OVERRIDE;
    // events:
    virtual void selectEvent(QMouseEvent *event, bool additive, const QVariant &details, bool *selectionStateChanged) Q_DECL_OVERRIDE;
    virtual void deselectEvent(bool *selectionStateChanged) Q_DECL_OVERRIDE;
    // mouse events:
    virtual void mousePressEvent(QMouseEvent *event, const QVariant &details) Q_DECL_OVERRIDE;
    virtual void mouseMoveEvent(QMouseEvent *event, const QPointF &startPos) Q_DECL_OVERRIDE;
    virtual void mouseReleaseEvent(QMouseEvent *event, const QPointF &startPos) Q_DECL_OVERRIDE;
    virtual void wheelEvent(QWheelEvent *event) Q_DECL_OVERRIDE;

    // non-virtual methods:
    void setupTickVectors();
    QPen getBasePen() const;
    QPen getTickPen() const;
    QPen getSubTickPen() const;
    QFont getTickLabelFont() const;
    QFont getLabelFont() const;
    QColor getTickLabelColor() const;
    QColor getLabelColor() const;

private:
    Q_DISABLE_COPY(QCPAxis)

    friend class QCustomPlot;
    friend class QCPGrid;
    friend class QCPAxisRect;
};
Q_DECLARE_OPERATORS_FOR_FLAGS(QCPAxis::SelectableParts)
Q_DECLARE_OPERATORS_FOR_FLAGS(QCPAxis::AxisTypes)
Q_DECLARE_METATYPE(QCPAxis::AxisType)
Q_DECLARE_METATYPE(QCPAxis::LabelSide)
Q_DECLARE_METATYPE(QCPAxis::ScaleType)
Q_DECLARE_METATYPE(QCPAxis::SelectablePart)


class QCPAxisPainterPrivate
{
public:
    explicit QCPAxisPainterPrivate(QCustomPlot *parentPlot);
    virtual ~QCPAxisPainterPrivate();

    virtual void draw(QCPPainter *painter);
    virtual int size();
    void clearCache();

    QRect axisSelectionBox() const { return mAxisSelectionBox; }
    QRect tickLabelsSelectionBox() const { return mTickLabelsSelectionBox; }
    QRect labelSelectionBox() const { return mLabelSelectionBox; }

    // public property members:
    QCPAxis::AxisType type;
    QPen basePen;
    QCPLineEnding lowerEnding, upperEnding; // directly accessed by QCPAxis setters/getters
    int labelPadding; // directly accessed by QCPAxis setters/getters
    QFont labelFont;
    QColor labelColor;
    QString label;
    int tickLabelPadding; // directly accessed by QCPAxis setters/getters
    double tickLabelRotation; // directly accessed by QCPAxis setters/getters
    QCPAxis::LabelSide tickLabelSide; // directly accessed by QCPAxis setters/getters
    bool substituteExponent;
    bool numberMultiplyCross; // directly accessed by QCPAxis setters/getters
    int tickLengthIn, tickLengthOut, subTickLengthIn, subTickLengthOut; // directly accessed by QCPAxis setters/getters
    QPen tickPen, subTickPen;
    QFont tickLabelFont;
    QColor tickLabelColor;
    QRect axisRect, viewportRect;
    int offset; // directly accessed by QCPAxis setters/getters
    bool abbreviateDecimalPowers;
    bool reversedEndings;

    QVector<double> subTickPositions;
    QVector<double> tickPositions;
    QVector<QString> tickLabels;

protected:
    struct CachedLabel
    {
        QPointF offset;
        QPixmap pixmap;
    };
    struct TickLabelData
    {
        QString basePart, expPart, suffixPart;
        QRect baseBounds, expBounds, suffixBounds, totalBounds, rotatedTotalBounds;
        QFont baseFont, expFont;
    };
    QCustomPlot *mParentPlot;
    QByteArray mLabelParameterHash; // to determine whether mLabelCache needs to be cleared due to changed parameters
    QCache<QString, CachedLabel> mLabelCache;
    QRect mAxisSelectionBox, mTickLabelsSelectionBox, mLabelSelectionBox;

    virtual QByteArray generateLabelParameterHash() const;

    virtual void placeTickLabel(QCPPainter *painter, double position, int distanceToAxis, const QString &text, QSize *tickLabelsSize);
    virtual void drawTickLabel(QCPPainter *painter, double x, double y, const TickLabelData &labelData) const;
    virtual TickLabelData getTickLabelData(const QFont &font, const QString &text) const;
    virtual QPointF getTickLabelDrawOffset(const TickLabelData &labelData) const;
    virtual void getMaxTickLabelSize(const QFont &font, const QString &text, QSize *tickLabelsSize) const;
};

/* end of 'src/axis/axis.h' */


/* including file 'src/scatterstyle.h'     */
/* modified 2021-03-29T02:30:44, size 7275 */

class QCP_LIB_DECL QCPScatterStyle
{
    Q_GADGET
public:
    /*!
    Represents the various properties of a scatter style instance. For example, this enum is used
    to specify which properties of \ref QCPSelectionDecorator::setScatterStyle will be used when
    highlighting selected data points.

    Specific scatter properties can be transferred between \ref QCPScatterStyle instances via \ref
    setFromOther.
  */
    enum ScatterProperty { spNone  = 0x00  ///< <tt>0x00</tt> None
                           ,spPen   = 0x01  ///< <tt>0x01</tt> The pen property, see \ref setPen
                           ,spBrush = 0x02  ///< <tt>0x02</tt> The brush property, see \ref setBrush
                           ,spSize  = 0x04  ///< <tt>0x04</tt> The size property, see \ref setSize
                           ,spShape = 0x08  ///< <tt>0x08</tt> The shape property, see \ref setShape
                           ,spAll   = 0xFF  ///< <tt>0xFF</tt> All properties
    };
    Q_ENUMS(ScatterProperty)
    Q_FLAGS(ScatterProperties)
    Q_DECLARE_FLAGS(ScatterProperties, ScatterProperty)

    /*!
    Defines the shape used for scatter points.

    On plottables/items that draw scatters, the sizes of these visualizations (with exception of
    \ref ssDot and \ref ssPixmap) can be controlled with the \ref setSize function. Scatters are
    drawn with the pen and brush specified with \ref setPen and \ref setBrush.
  */
    enum ScatterShape { ssNone       ///< no scatter symbols are drawn (e.g. in QCPGraph, data only represented with lines)
                        ,ssDot       ///< \enumimage{ssDot.png} a single pixel (use \ref ssDisc or \ref ssCircle if you want a round shape with a certain radius)
                        ,ssCross     ///< \enumimage{ssCross.png} a cross
                        ,ssPlus      ///< \enumimage{ssPlus.png} a plus
                        ,ssCircle    ///< \enumimage{ssCircle.png} a circle
                        ,ssDisc      ///< \enumimage{ssDisc.png} a circle which is filled with the pen's color (not the brush as with ssCircle)
                        ,ssSquare    ///< \enumimage{ssSquare.png} a square
                        ,ssDiamond   ///< \enumimage{ssDiamond.png} a diamond
                        ,ssStar      ///< \enumimage{ssStar.png} a star with eight arms, i.e. a combination of cross and plus
                        ,ssTriangle  ///< \enumimage{ssTriangle.png} an equilateral triangle, standing on baseline
                        ,ssTriangleInverted ///< \enumimage{ssTriangleInverted.png} an equilateral triangle, standing on corner
                        ,ssCrossSquare      ///< \enumimage{ssCrossSquare.png} a square with a cross inside
                        ,ssPlusSquare       ///< \enumimage{ssPlusSquare.png} a square with a plus inside
                        ,ssCrossCircle      ///< \enumimage{ssCrossCircle.png} a circle with a cross inside
                        ,ssPlusCircle       ///< \enumimage{ssPlusCircle.png} a circle with a plus inside
                        ,ssPeace     ///< \enumimage{ssPeace.png} a circle, with one vertical and two downward diagonal lines
                        ,ssPixmap    ///< a custom pixmap specified by \ref setPixmap, centered on the data point coordinates
                        ,ssCustom    ///< custom painter operations are performed per scatter (As QPainterPath, see \ref setCustomPath)
    };
    Q_ENUMS(ScatterShape)

    QCPScatterStyle();
    QCPScatterStyle(ScatterShape shape, double size=6);
    QCPScatterStyle(ScatterShape shape, const QColor &color, double size);
    QCPScatterStyle(ScatterShape shape, const QColor &color, const QColor &fill, double size);
    QCPScatterStyle(ScatterShape shape, const QPen &pen, const QBrush &brush, double size);
    QCPScatterStyle(const QPixmap &pixmap);
    QCPScatterStyle(const QPainterPath &customPath, const QPen &pen, const QBrush &brush=Qt::NoBrush, double size=6);

    // getters:
    double size() const { return mSize; }
    ScatterShape shape() const { return mShape; }
    QPen pen() const { return mPen; }
    QBrush brush() const { return mBrush; }
    QPixmap pixmap() const { return mPixmap; }
    QPainterPath customPath() const { return mCustomPath; }

    // setters:
    void setFromOther(const QCPScatterStyle &other, ScatterProperties properties);
    void setSize(double size);
    void setShape(ScatterShape shape);
    void setPen(const QPen &pen);
    void setBrush(const QBrush &brush);
    void setPixmap(const QPixmap &pixmap);
    void setCustomPath(const QPainterPath &customPath);

    // non-property methods:
    bool isNone() const { return mShape == ssNone; }
    bool isPenDefined() const { return mPenDefined; }
    void undefinePen();
    void applyTo(QCPPainter *painter, const QPen &defaultPen) const;
    void drawShape(QCPPainter *painter, const QPointF &pos) const;
    void drawShape(QCPPainter *painter, double x, double y) const;

protected:
    // property members:
    double mSize;
    ScatterShape mShape;
    QPen mPen;
    QBrush mBrush;
    QPixmap mPixmap;
    QPainterPath mCustomPath;

    // non-property members:
    bool mPenDefined;
};
Q_DECLARE_TYPEINFO(QCPScatterStyle, Q_MOVABLE_TYPE);
Q_DECLARE_OPERATORS_FOR_FLAGS(QCPScatterStyle::ScatterProperties)
Q_DECLARE_METATYPE(QCPScatterStyle::ScatterProperty)
Q_DECLARE_METATYPE(QCPScatterStyle::ScatterShape)

/* end of 'src/scatterstyle.h' */


/* including file 'src/datacontainer.h'     */
/* modified 2021-03-29T02:30:44, size 34070 */

/*! \relates QCPDataContainer
  Returns whether the sort key of \a a is less than the sort key of \a b.

  \see QCPDataContainer::sort
*/
template <class DataType>
inline bool qcpLessThanSortKey(const DataType &a, const DataType &b) { return a.sortKey() < b.sortKey(); }

template <class DataType>
class QCPDataContainer // no QCP_LIB_DECL, template class ends up in header (cpp included below)
{
public:
    typedef typename QVector<DataType>::const_iterator const_iterator;
    typedef typename QVector<DataType>::iterator iterator;

    QCPDataContainer();

    // getters:
    int size() const { return mData.size()-mPreallocSize; }
    bool isEmpty() const { return size() == 0; }
    bool autoSqueeze() const { return mAutoSqueeze; }

    // setters:
    void setAutoSqueeze(bool enabled);

    // non-virtual methods:
    void set(const QCPDataContainer<DataType> &data);
    void set(const QVector<DataType> &data, bool alreadySorted=false);
    void add(const QCPDataContainer<DataType> &data);
    void add(const QVector<DataType> &data, bool alreadySorted=false);
    void add(const DataType &data);
    void removeBefore(double sortKey);
    void removeAfter(double sortKey);
    void remove(double sortKeyFrom, double sortKeyTo);
    void remove(double sortKey);
    void clear();
    void sort();
    void squeeze(bool preAllocation=true, bool postAllocation=true);

    const_iterator constBegin() const { return mData.constBegin()+mPreallocSize; }
    const_iterator constEnd() const { return mData.constEnd(); }
    iterator begin() { return mData.begin()+mPreallocSize; }
    iterator end() { return mData.end(); }
    const_iterator findBegin(double sortKey, bool expandedRange=true) const;
    const_iterator findEnd(double sortKey, bool expandedRange=true) const;
    const_iterator at(int index) const { return constBegin()+qBound(0, index, size()); }
    QCPRange keyRange(bool &foundRange, QCP::SignDomain signDomain=QCP::sdBoth);
    QCPRange valueRange(bool &foundRange, QCP::SignDomain signDomain=QCP::sdBoth, const QCPRange &inKeyRange=QCPRange());
    QCPDataRange dataRange() const { return QCPDataRange(0, size()); }
    void limitIteratorsToDataRange(const_iterator &begin, const_iterator &end, const QCPDataRange &dataRange) const;

protected:
    // property members:
    bool mAutoSqueeze;

    // non-property memebers:
    QVector<DataType> mData;
    int mPreallocSize;
    int mPreallocIteration;

    // non-virtual methods:
    void preallocateGrow(int minimumPreallocSize);
    void performAutoSqueeze();
};



// include implementation in header since it is a class template:
////////////////////////////////////////////////////////////////////////////////////////////////////
//////////////////// QCPDataContainer
////////////////////////////////////////////////////////////////////////////////////////////////////

/*! \class QCPDataContainer
  \brief The generic data container for one-dimensional plottables

  This class template provides a fast container for data storage of one-dimensional data. The data
  type is specified as template parameter (called \a DataType in the following) and must provide
  some methods as described in the \ref qcpdatacontainer-datatype "next section".

  The data is stored in a sorted fashion, which allows very quick lookups by the sorted key as well
  as retrieval of ranges (see \ref findBegin, \ref findEnd, \ref keyRange) using binary search. The
  container uses a preallocation and a postallocation scheme, such that appending and prepending
  data (with respect to the sort key) is very fast and minimizes reallocations. If data is added
  which needs to be inserted between existing keys, the merge usually can be done quickly too,
  using the fact that existing data is always sorted. The user can further improve performance by
  specifying that added data is already itself sorted by key, if he can guarantee that this is the
  case (see for example \ref add(const QVector<DataType> &data, bool alreadySorted)).

  The data can be accessed with the provided const iterators (\ref constBegin, \ref constEnd). If
  it is necessary to alter existing data in-place, the non-const iterators can be used (\ref begin,
  \ref end). Changing data members that are not the sort key (for most data types called \a key) is
  safe from the container's perspective.

  Great care must be taken however if the sort key is modified through the non-const iterators. For
  performance reasons, the iterators don't automatically cause a re-sorting upon their
  manipulation. It is thus the responsibility of the user to leave the container in a sorted state
  when finished with the data manipulation, before calling any other methods on the container. A
  complete re-sort (e.g. after finishing all sort key manipulation) can be done by calling \ref
  sort. Failing to do so can not be detected by the container efficiently and will cause both
  rendering artifacts and potential data loss.

  Implementing one-dimensional plottables that make use of a \ref QCPDataContainer<T> is usually
  done by subclassing from \ref QCPAbstractPlottable1D "QCPAbstractPlottable1D<T>", which
  introduces an according \a mDataContainer member and some convenience methods.

  \section qcpdatacontainer-datatype Requirements for the DataType template parameter

  The template parameter <tt>DataType</tt> is the type of the stored data points. It must be
  trivially copyable and have the following public methods, preferably inline:

  \li <tt>double sortKey() const</tt>\n Returns the member variable of this data point that is the
  sort key, defining the ordering in the container. Often this variable is simply called \a key.

  \li <tt>static DataType fromSortKey(double sortKey)</tt>\n Returns a new instance of the data
  type initialized with its sort key set to \a sortKey.

  \li <tt>static bool sortKeyIsMainKey()</tt>\n Returns true if the sort key is equal to the main
  key (see method \c mainKey below). For most plottables this is the case. It is not the case for
  example for \ref QCPCurve, which uses \a t as sort key and \a key as main key. This is the reason
  why QCPCurve unlike QCPGraph can display parametric curves with loops.

  \li <tt>double mainKey() const</tt>\n Returns the variable of this data point considered the main
  key. This is commonly the variable that is used as the coordinate of this data point on the key
  axis of the plottable. This method is used for example when determining the automatic axis
  rescaling of key axes (\ref QCPAxis::rescale).

  \li <tt>double mainValue() const</tt>\n Returns the variable of this data point considered the
  main value. This is commonly the variable that is used as the coordinate of this data point on
  the value axis of the plottable.

  \li <tt>QCPRange valueRange() const</tt>\n Returns the range this data point spans in the value
  axis coordinate. If the data is single-valued (e.g. QCPGraphData), this is simply a range with
  both lower and upper set to the main data point value. However if the data points can represent
  multiple values at once (e.g QCPFinancialData with its \a high, \a low, \a open and \a close
  values at each \a key) this method should return the range those values span. This method is used
  for example when determining the automatic axis rescaling of value axes (\ref
  QCPAxis::rescale).
*/

/* start documentation of inline functions */

/*! \fn int QCPDataContainer<DataType>::size() const

  Returns the number of data points in the container.
*/

/*! \fn bool QCPDataContainer<DataType>::isEmpty() const

  Returns whether this container holds no data points.
*/

/*! \fn QCPDataContainer::const_iterator QCPDataContainer<DataType>::constBegin() const

  Returns a const iterator to the first data point in this container.
*/

/*! \fn QCPDataContainer::const_iterator QCPDataContainer<DataType>::constEnd() const

  Returns a const iterator to the element past the last data point in this container.
*/

/*! \fn QCPDataContainer::iterator QCPDataContainer<DataType>::begin() const

  Returns a non-const iterator to the first data point in this container.

  You can manipulate the data points in-place through the non-const iterators, but great care must
  be taken when manipulating the sort key of a data point, see \ref sort, or the detailed
  description of this class.
*/

/*! \fn QCPDataContainer::iterator QCPDataContainer<DataType>::end() const

  Returns a non-const iterator to the element past the last data point in this container.

  You can manipulate the data points in-place through the non-const iterators, but great care must
  be taken when manipulating the sort key of a data point, see \ref sort, or the detailed
  description of this class.
*/

/*! \fn QCPDataContainer::const_iterator QCPDataContainer<DataType>::at(int index) const

  Returns a const iterator to the element with the specified \a index. If \a index points beyond
  the available elements in this container, returns \ref constEnd, i.e. an iterator past the last
  valid element.

  You can use this method to easily obtain iterators from a \ref QCPDataRange, see the \ref
  dataselection-accessing "data selection page" for an example.
*/

/*! \fn QCPDataRange QCPDataContainer::dataRange() const

  Returns a \ref QCPDataRange encompassing the entire data set of this container. This means the
  begin index of the returned range is 0, and the end index is \ref size.
*/

/* end documentation of inline functions */

/*!
  Constructs a QCPDataContainer used for plottable classes that represent a series of key-sorted
  data
*/
template <class DataType>
QCPDataContainer<DataType>::QCPDataContainer() :
    mAutoSqueeze(true),
    mPreallocSize(0),
    mPreallocIteration(0)
{
}

/*!
  Sets whether the container automatically decides when to release memory from its post- and
  preallocation pools when data points are removed. By default this is enabled and for typical
  applications shouldn't be changed.

  If auto squeeze is disabled, you can manually decide when to release pre-/postallocation with
  \ref squeeze.
*/
template <class DataType>
void QCPDataContainer<DataType>::setAutoSqueeze(bool enabled)
{
    if (mAutoSqueeze != enabled)
    {
        mAutoSqueeze = enabled;
        if (mAutoSqueeze)
            performAutoSqueeze();
    }
}

/*! \overload

  Replaces the current data in this container with the provided \a data.

  \see add, remove
*/
template <class DataType>
void QCPDataContainer<DataType>::set(const QCPDataContainer<DataType> &data)
{
    clear();
    add(data);
}

/*! \overload

  Replaces the current data in this container with the provided \a data

  If you can guarantee that the data points in \a data have ascending order with respect to the
  DataType's sort key, set \a alreadySorted to true to avoid an unnecessary sorting run.

  \see add, remove
*/
template <class DataType>
void QCPDataContainer<DataType>::set(const QVector<DataType> &data, bool alreadySorted)
{
    mData = data;
    mPreallocSize = 0;
    mPreallocIteration = 0;
    if (!alreadySorted)
        sort();
}

/*! \overload

  Adds the provided \a data to the current data in this container.

  \see set, remove
*/
template <class DataType>
void QCPDataContainer<DataType>::add(const QCPDataContainer<DataType> &data)
{
    if (data.isEmpty())
        return;

    const int n = data.size();
    const int oldSize = size();

    if (oldSize > 0 && !qcpLessThanSortKey<DataType>(*constBegin(), *(data.constEnd()-1))) // prepend if new data keys are all smaller than or equal to existing ones
    {
        if (mPreallocSize < n)
            preallocateGrow(n);
        mPreallocSize -= n;
        std::copy(data.constBegin(), data.constEnd(), begin());
    } else // don't need to prepend, so append and merge if necessary
    {
        mData.resize(mData.size()+n);
        std::copy(data.constBegin(), data.constEnd(), end()-n);
        if (oldSize > 0 && !qcpLessThanSortKey<DataType>(*(constEnd()-n-1), *(constEnd()-n))) // if appended range keys aren't all greater than existing ones, merge the two partitions
            std::inplace_merge(begin(), end()-n, end(), qcpLessThanSortKey<DataType>);
    }
}

/*!
  Adds the provided data points in \a data to the current data.

  If you can guarantee that the data points in \a data have ascending order with respect to the
  DataType's sort key, set \a alreadySorted to true to avoid an unnecessary sorting run.

  \see set, remove
*/
template <class DataType>
void QCPDataContainer<DataType>::add(const QVector<DataType> &data, bool alreadySorted)
{
    if (data.isEmpty())
        return;
    if (isEmpty())
    {
        set(data, alreadySorted);
        return;
    }

    const int n = data.size();
    const int oldSize = size();

    if (alreadySorted && oldSize > 0 && !qcpLessThanSortKey<DataType>(*constBegin(), *(data.constEnd()-1))) // prepend if new data is sorted and keys are all smaller than or equal to existing ones
    {
        if (mPreallocSize < n)
            preallocateGrow(n);
        mPreallocSize -= n;
        std::copy(data.constBegin(), data.constEnd(), begin());
    } else // don't need to prepend, so append and then sort and merge if necessary
    {
        mData.resize(mData.size()+n);
        std::copy(data.constBegin(), data.constEnd(), end()-n);
        if (!alreadySorted) // sort appended subrange if it wasn't already sorted
            std::sort(end()-n, end(), qcpLessThanSortKey<DataType>);
        if (oldSize > 0 && !qcpLessThanSortKey<DataType>(*(constEnd()-n-1), *(constEnd()-n))) // if appended range keys aren't all greater than existing ones, merge the two partitions
            std::inplace_merge(begin(), end()-n, end(), qcpLessThanSortKey<DataType>);
    }
}

/*! \overload

  Adds the provided single data point to the current data.

  \see remove
*/
template <class DataType>
void QCPDataContainer<DataType>::add(const DataType &data)
{
    if (isEmpty() || !qcpLessThanSortKey<DataType>(data, *(constEnd()-1))) // quickly handle appends if new data key is greater or equal to existing ones
    {
        mData.append(data);
    } else if (qcpLessThanSortKey<DataType>(data, *constBegin()))  // quickly handle prepends using preallocated space
    {
        if (mPreallocSize < 1)
            preallocateGrow(1);
        --mPreallocSize;
        *begin() = data;
    } else // handle inserts, maintaining sorted keys
    {
        QCPDataContainer<DataType>::iterator insertionPoint = std::lower_bound(begin(), end(), data, qcpLessThanSortKey<DataType>);
        mData.insert(insertionPoint, data);
    }
}

/*!
  Removes all data points with (sort-)keys smaller than or equal to \a sortKey.

  \see removeAfter, remove, clear
*/
template <class DataType>
void QCPDataContainer<DataType>::removeBefore(double sortKey)
{
    QCPDataContainer<DataType>::iterator it = begin();
    QCPDataContainer<DataType>::iterator itEnd = std::lower_bound(begin(), end(), DataType::fromSortKey(sortKey), qcpLessThanSortKey<DataType>);
    mPreallocSize += int(itEnd-it); // don't actually delete, just add it to the preallocated block (if it gets too large, squeeze will take care of it)
    if (mAutoSqueeze)
        performAutoSqueeze();
}

/*!
  Removes all data points with (sort-)keys greater than or equal to \a sortKey.

  \see removeBefore, remove, clear
*/
template <class DataType>
void QCPDataContainer<DataType>::removeAfter(double sortKey)
{
    QCPDataContainer<DataType>::iterator it = std::upper_bound(begin(), end(), DataType::fromSortKey(sortKey), qcpLessThanSortKey<DataType>);
    QCPDataContainer<DataType>::iterator itEnd = end();
    mData.erase(it, itEnd); // typically adds it to the postallocated block
    if (mAutoSqueeze)
        performAutoSqueeze();
}

/*!
  Removes all data points with (sort-)keys between \a sortKeyFrom and \a sortKeyTo. if \a
  sortKeyFrom is greater or equal to \a sortKeyTo, the function does nothing. To remove a single
  data point with known (sort-)key, use \ref remove(double sortKey).

  \see removeBefore, removeAfter, clear
*/
template <class DataType>
void QCPDataContainer<DataType>::remove(double sortKeyFrom, double sortKeyTo)
{
    if (sortKeyFrom >= sortKeyTo || isEmpty())
        return;

    QCPDataContainer<DataType>::iterator it = std::lower_bound(begin(), end(), DataType::fromSortKey(sortKeyFrom), qcpLessThanSortKey<DataType>);
    QCPDataContainer<DataType>::iterator itEnd = std::upper_bound(it, end(), DataType::fromSortKey(sortKeyTo), qcpLessThanSortKey<DataType>);
    mData.erase(it, itEnd);
    if (mAutoSqueeze)
        performAutoSqueeze();
}

/*! \overload

  Removes a single data point at \a sortKey. If the position is not known with absolute (binary)
  precision, consider using \ref remove(double sortKeyFrom, double sortKeyTo) with a small
  fuzziness interval around the suspected position, depeding on the precision with which the
  (sort-)key is known.

  \see removeBefore, removeAfter, clear
*/
template <class DataType>
void QCPDataContainer<DataType>::remove(double sortKey)
{
    QCPDataContainer::iterator it = std::lower_bound(begin(), end(), DataType::fromSortKey(sortKey), qcpLessThanSortKey<DataType>);
    if (it != end() && it->sortKey() == sortKey)
    {
        if (it == begin())
            ++mPreallocSize; // don't actually delete, just add it to the preallocated block (if it gets too large, squeeze will take care of it)
        else
            mData.erase(it);
    }
    if (mAutoSqueeze)
        performAutoSqueeze();
}

/*!
  Removes all data points.

  \see remove, removeAfter, removeBefore
*/
template <class DataType>
void QCPDataContainer<DataType>::clear()
{
    mData.clear();
    mPreallocIteration = 0;
    mPreallocSize = 0;
}

/*!
  Re-sorts all data points in the container by their sort key.

  When setting, adding or removing points using the QCPDataContainer interface (\ref set, \ref add,
  \ref remove, etc.), the container makes sure to always stay in a sorted state such that a full
  resort is never necessary. However, if you choose to directly manipulate the sort key on data
  points by accessing and modifying it through the non-const iterators (\ref begin, \ref end), it
  is your responsibility to bring the container back into a sorted state before any other methods
  are called on it. This can be achieved by calling this method immediately after finishing the
  sort key manipulation.
*/
template <class DataType>
void QCPDataContainer<DataType>::sort()
{
    std::sort(begin(), end(), qcpLessThanSortKey<DataType>);
}

/*!
  Frees all unused memory that is currently in the preallocation and postallocation pools.

  Note that QCPDataContainer automatically decides whether squeezing is necessary, if \ref
  setAutoSqueeze is left enabled. It should thus not be necessary to use this method for typical
  applications.

  The parameters \a preAllocation and \a postAllocation control whether pre- and/or post allocation
  should be freed, respectively.
*/
template <class DataType>
void QCPDataContainer<DataType>::squeeze(bool preAllocation, bool postAllocation)
{
    if (preAllocation)
    {
        if (mPreallocSize > 0)
        {
            std::copy(begin(), end(), mData.begin());
            mData.resize(size());
            mPreallocSize = 0;
        }
        mPreallocIteration = 0;
    }
    if (postAllocation)
        mData.squeeze();
}
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
